pensthiel/head-md-future-of-drawing/electronics/fritzing/shematic_schem.jpg

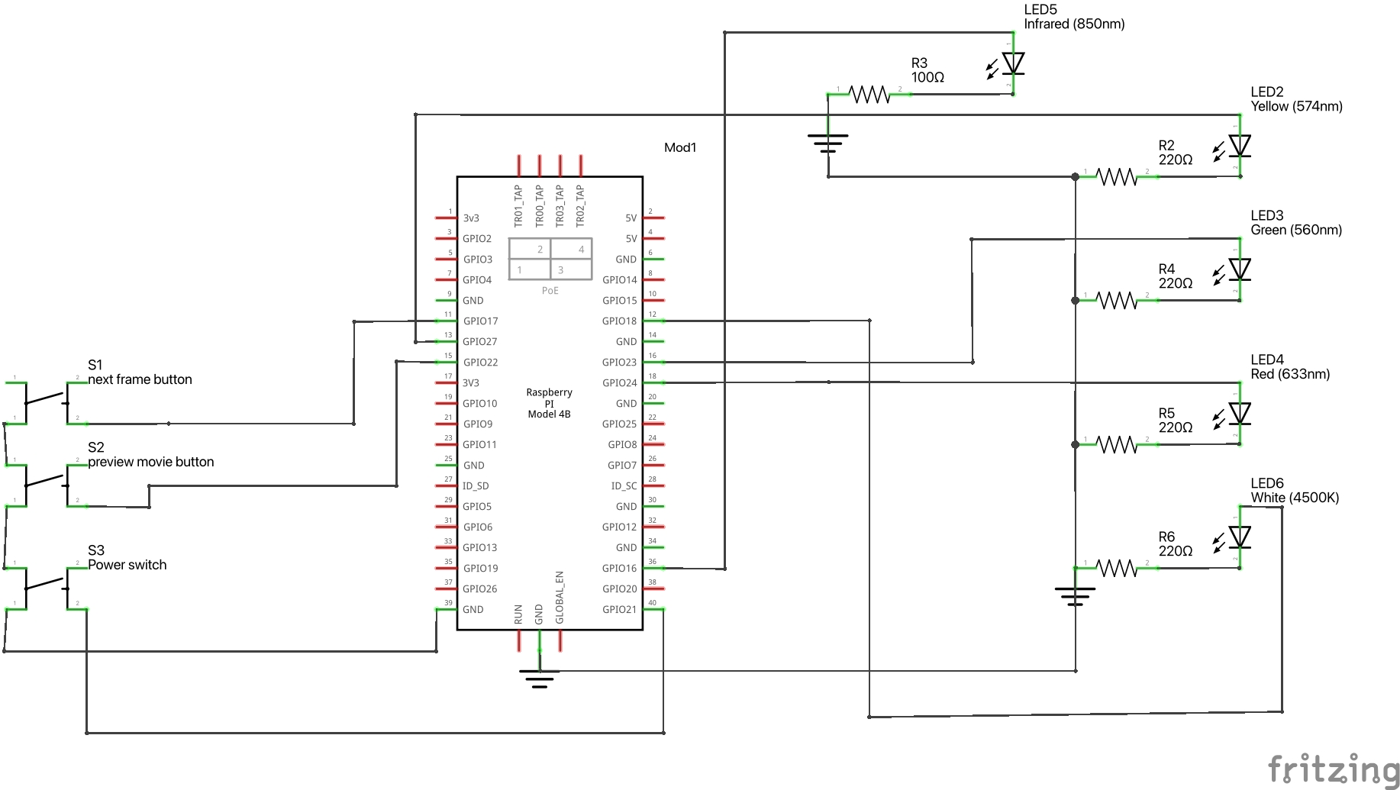
electronics/fritzing/shematic_schem.jpg
