pensthiel/head-md-future-of-drawing/electronics/photos/img_1540.jpg

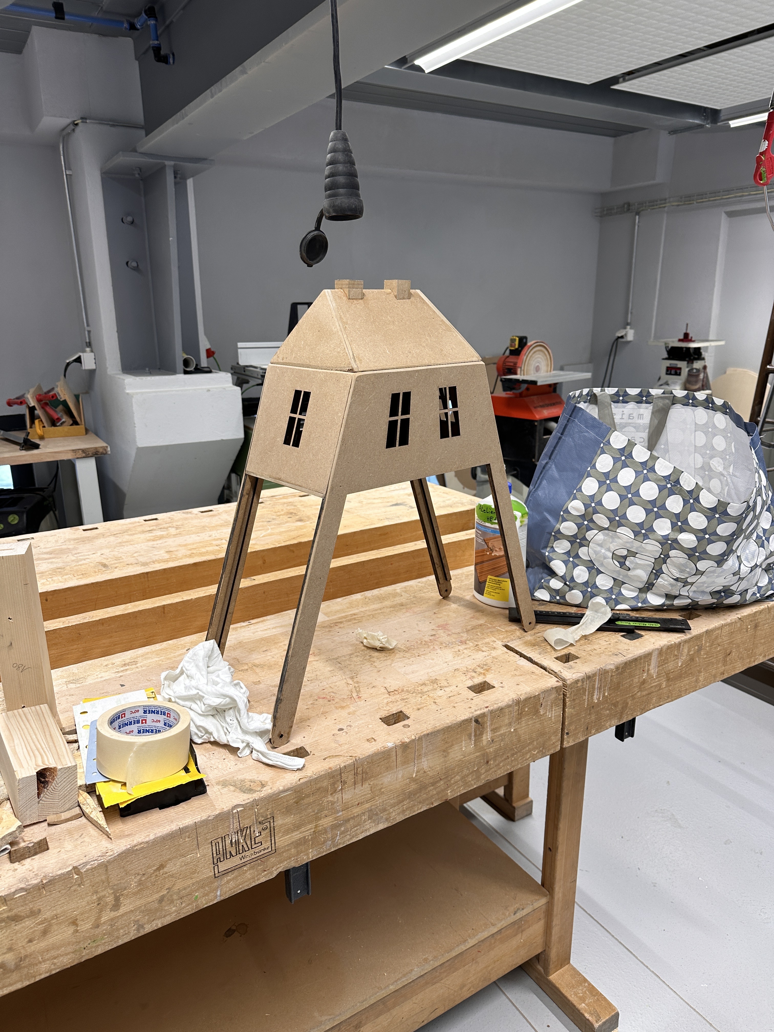
electronics/photos/img_1540.jpg
