pensthiel/head-md-future-of-drawing/electronics/photos/img_1547.jpg

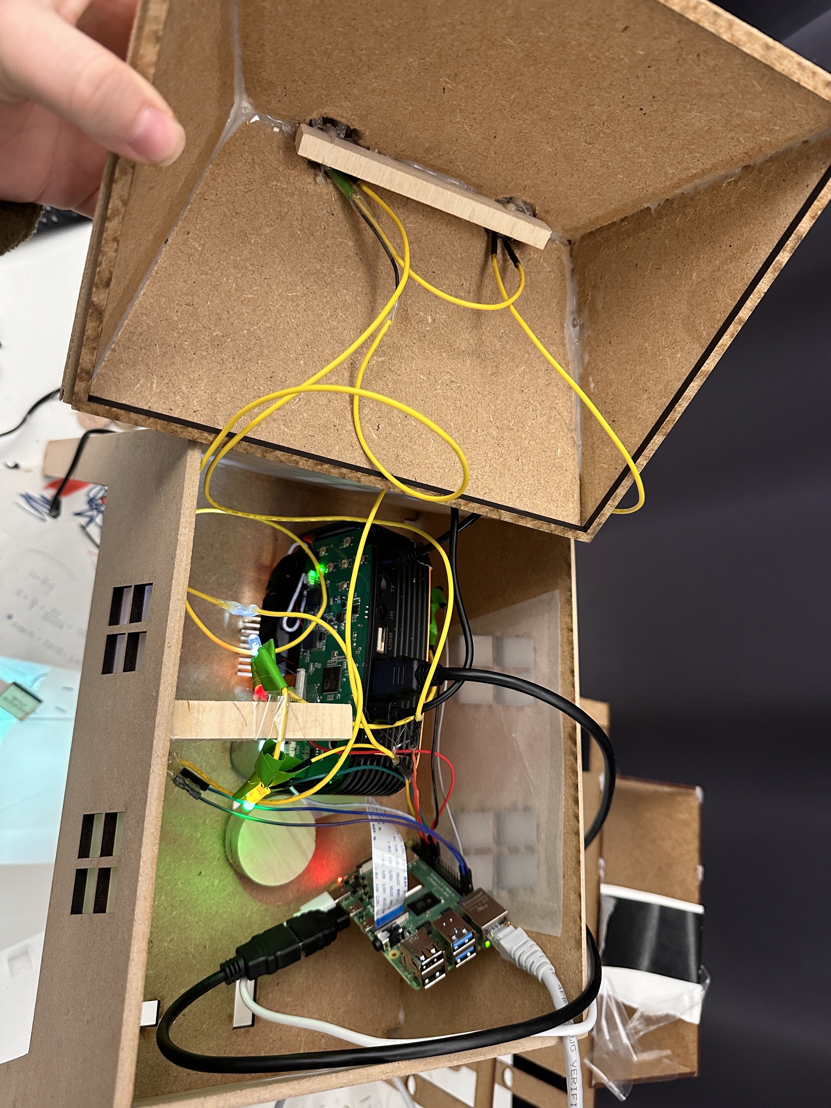
electronics/photos/img_1547.jpg
