pensthiel/head-md-future-of-drawing/expo/3d/Screenshot 2024-03-19 at 19.50.46.png

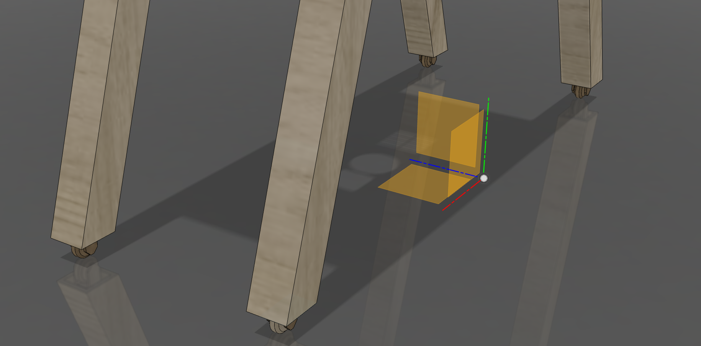
expo/3d/Screenshot 2024-03-19 at 19.50.46.png
