pensthiel/head-md-future-of-drawing/expo/3d/Screenshot 2024-03-19 at 19.51.49.png

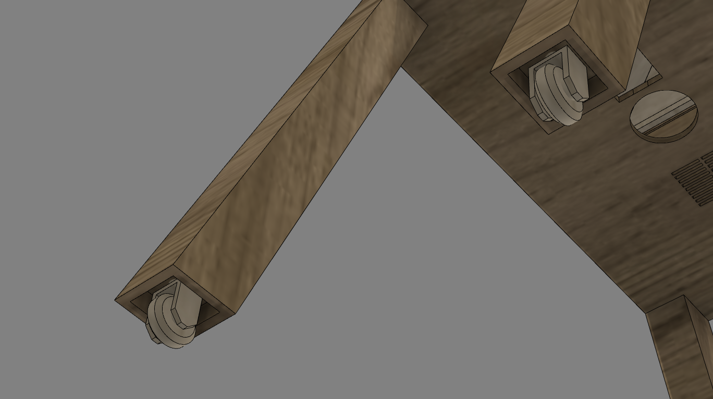
expo/3d/Screenshot 2024-03-19 at 19.51.49.png
