pensthiel/head-md-future-of-drawing/expo/3d/Screenshot 2024-03-19 at 19.52.38.png

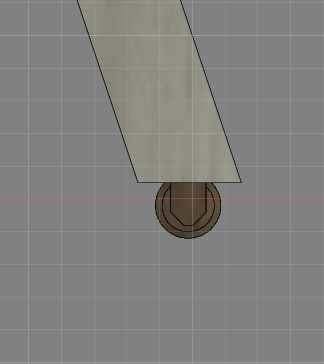
expo/3d/Screenshot 2024-03-19 at 19.52.38.png
