pensthiel/head-md-future-of-drawing/expo/3d/Screenshot 2024-03-20 at 10.05.37.png

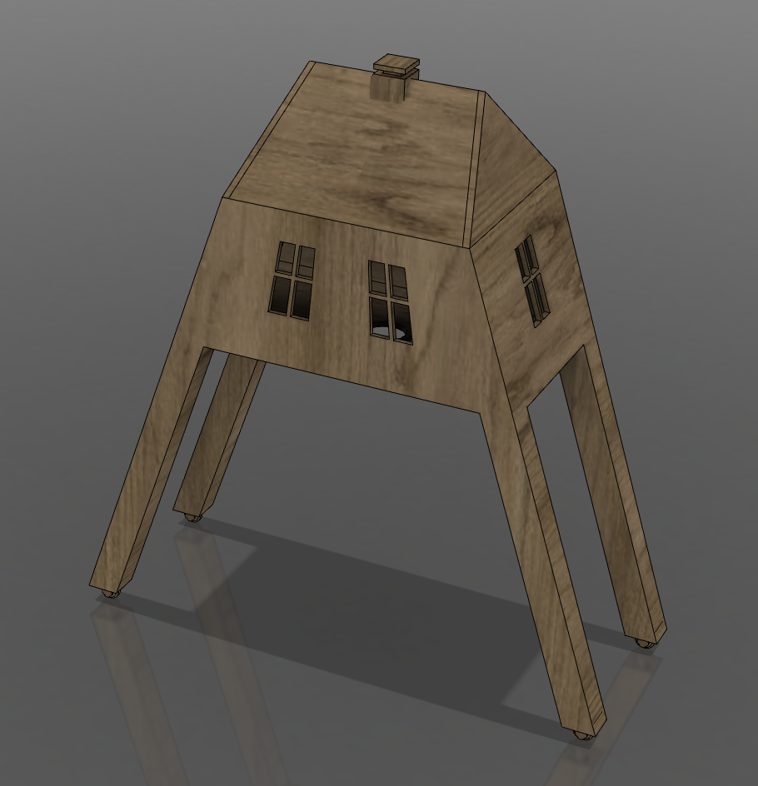
expo/3d/Screenshot 2024-03-20 at 10.05.37.png
