pensthiel/head-md-future-of-drawing/expo/3d/Screenshot 2024-04-22 at 10.32.50.png

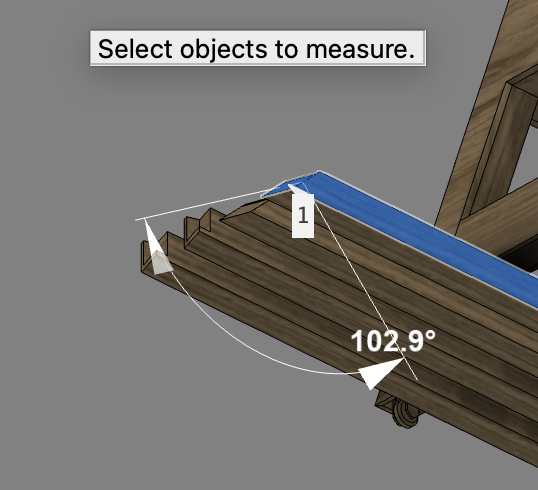
expo/3d/Screenshot 2024-04-22 at 10.32.50.png
