pensthiel/head-md-future-of-drawing/expo/shema/Untitled_Artwork.jpg

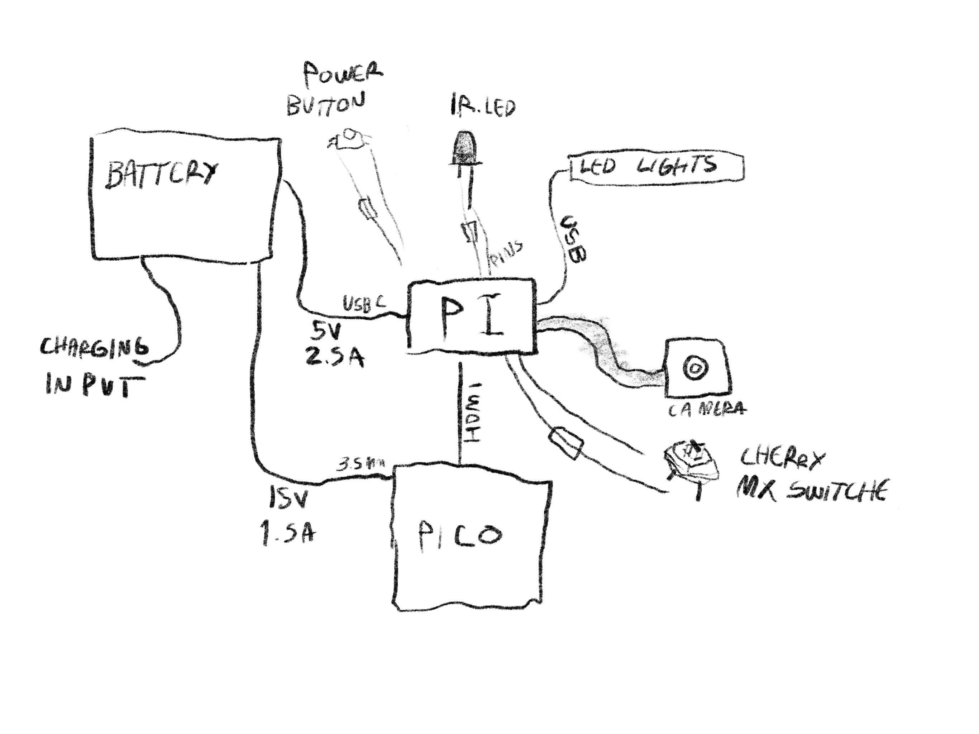
expo/shema/Untitled_Artwork.jpg
