pensthiel/head-md-future-of-drawing/namur/IMG_6740.jpg

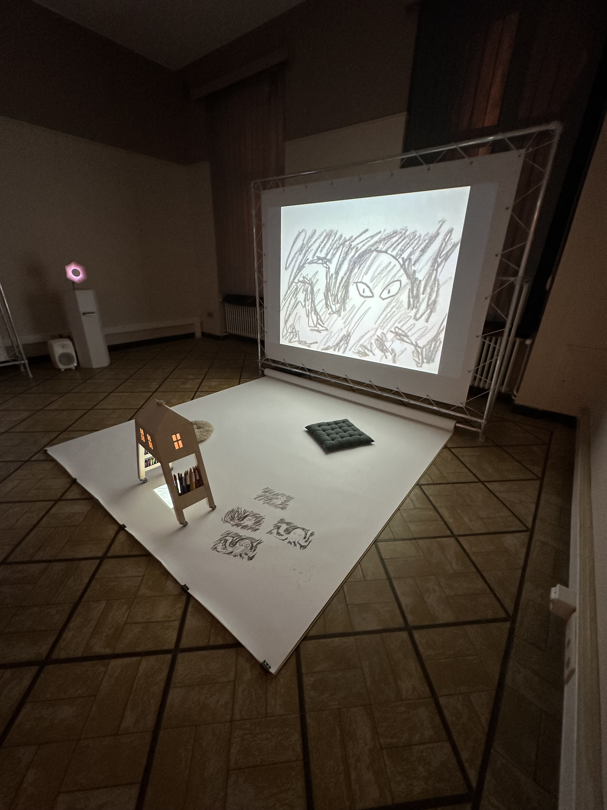
namur/IMG_6740.jpg
