pensthiel/head-md-future-of-drawing/namur/IMG_6743.jpg

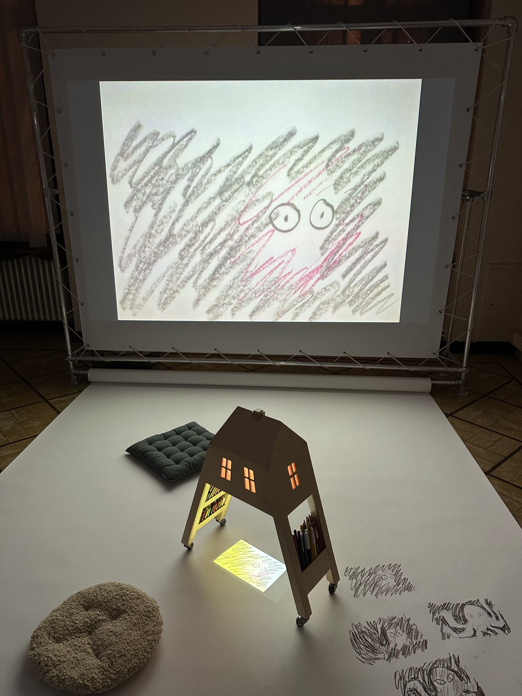
namur/IMG_6743.jpg
