pensthiel/head-md-future-of-drawing/namur/IMG_6744.jpg

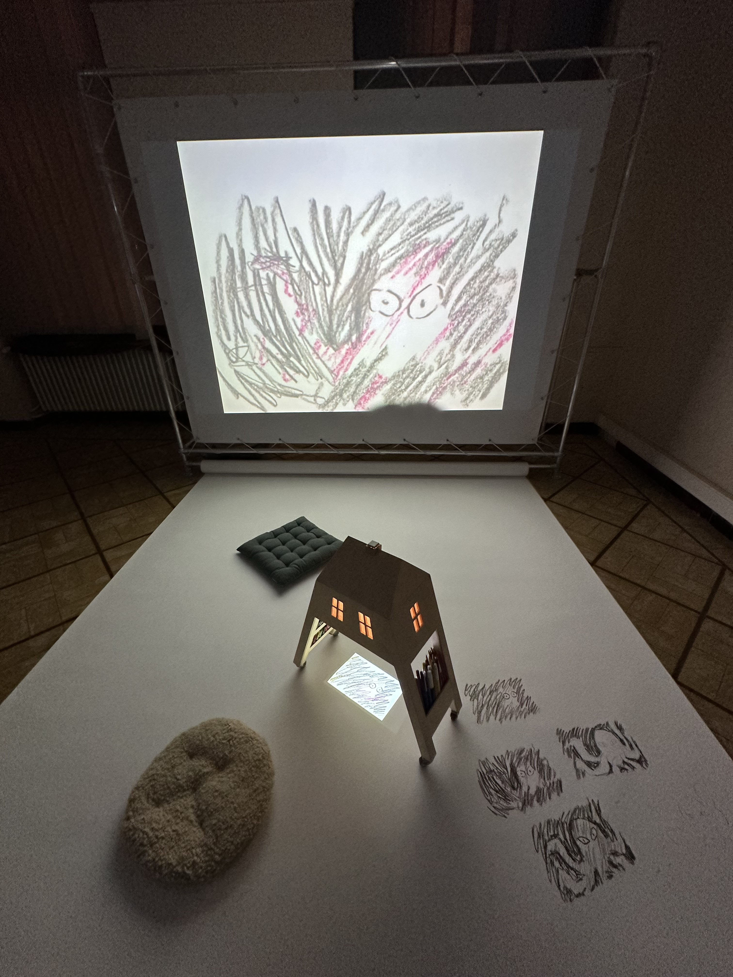
namur/IMG_6744.jpg
