pensthiel/head-md-future-of-drawing/namur/IMG_6754.jpg

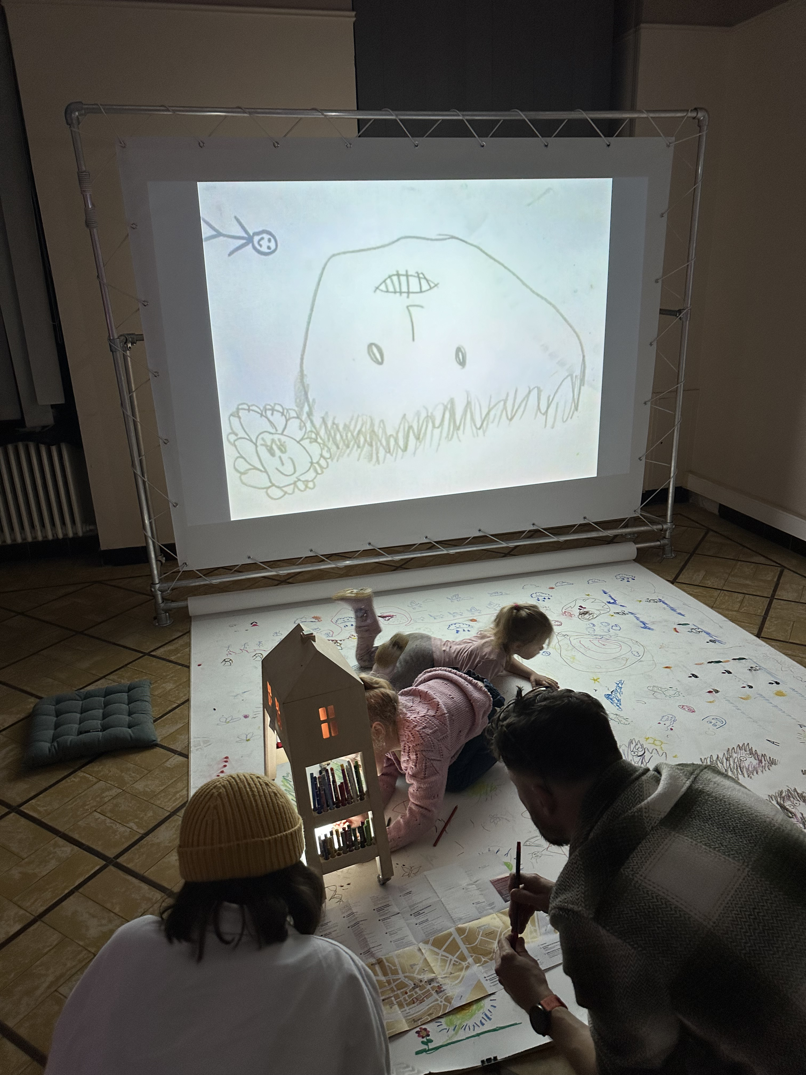
namur/IMG_6754.jpg
