pensthiel/head-md-future-of-drawing/namur/IMG_6794.jpg

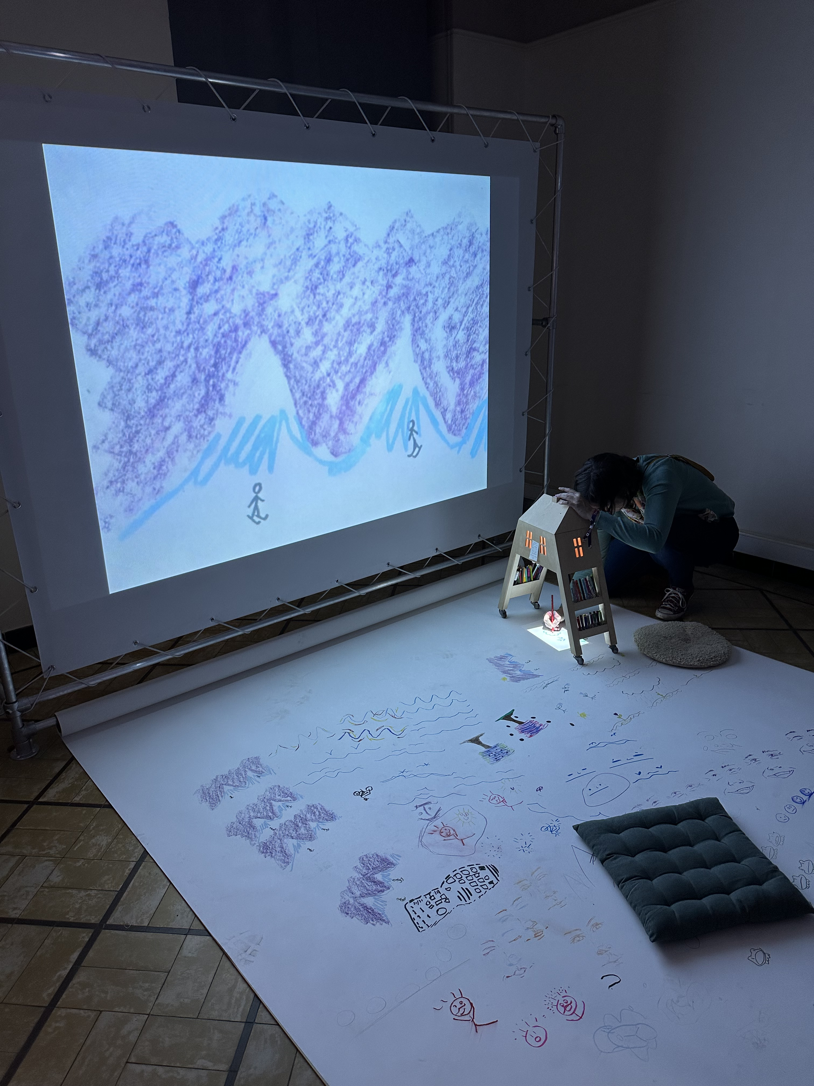
namur/IMG_6794.jpg
