pensthiel/head-md-future-of-drawing/namur/IMG_6797.jpg

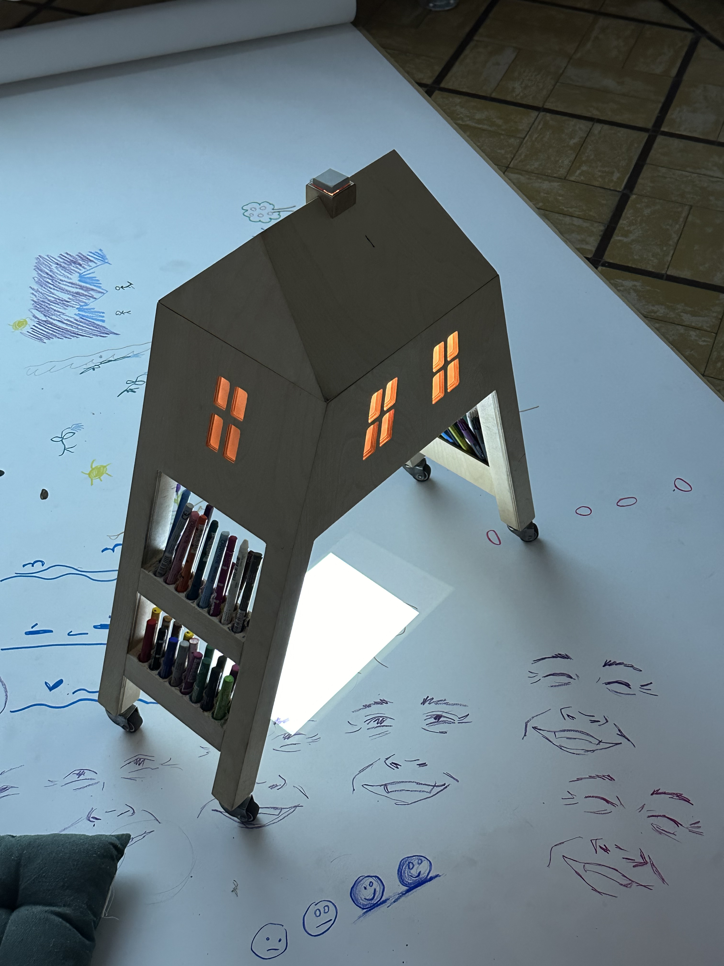
namur/IMG_6797.jpg
