pensthiel/head-md-future-of-drawing/namur/IMG_6829.jpg

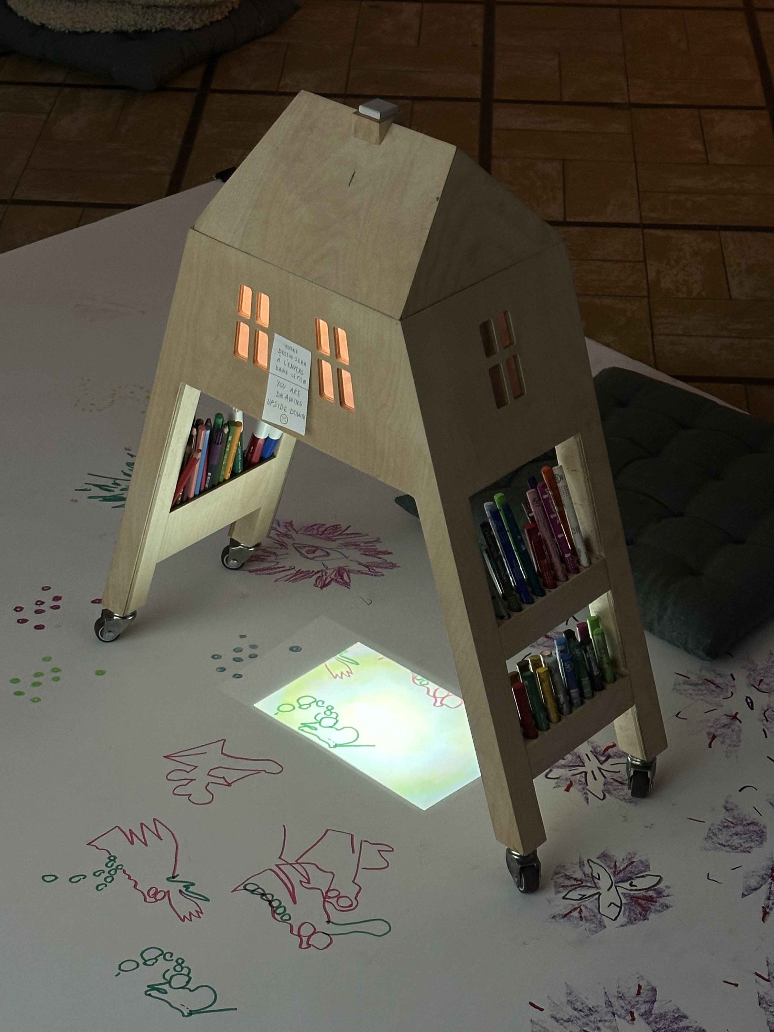
namur/IMG_6829.jpg
