pensthiel/head-md-future-of-drawing/namur/IMG_6830.jpg

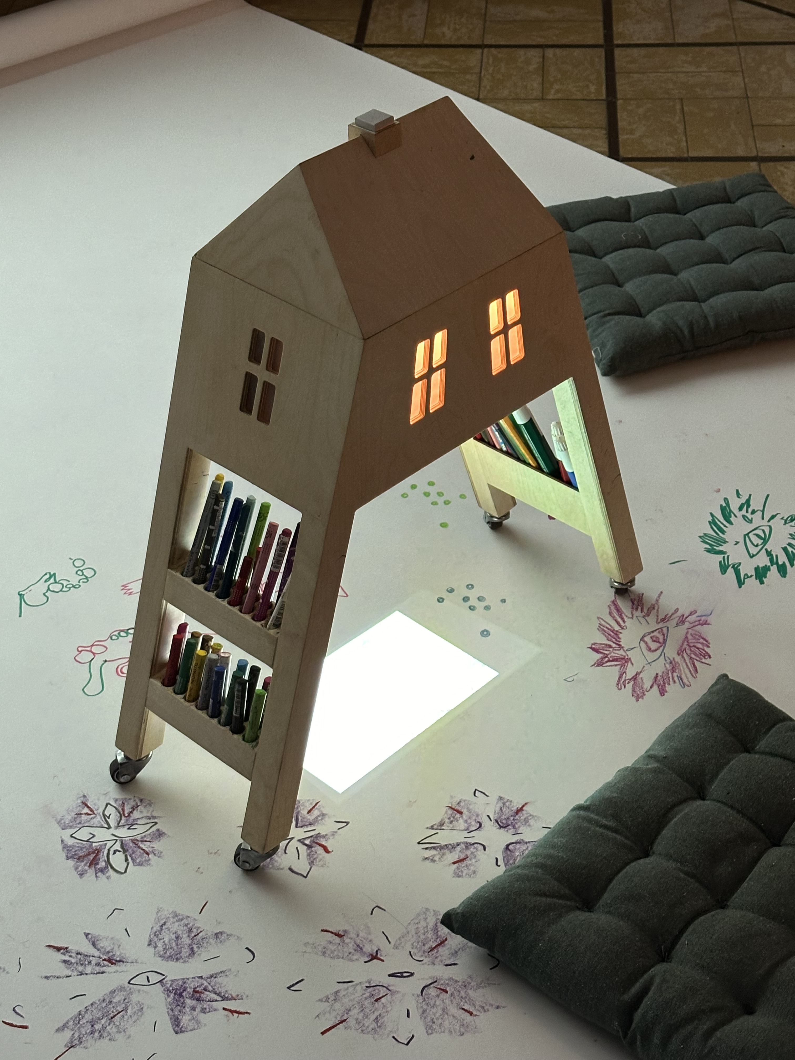
namur/IMG_6830.jpg
