pensthiel/head-md-future-of-drawing/namur/IMG_6961.jpg

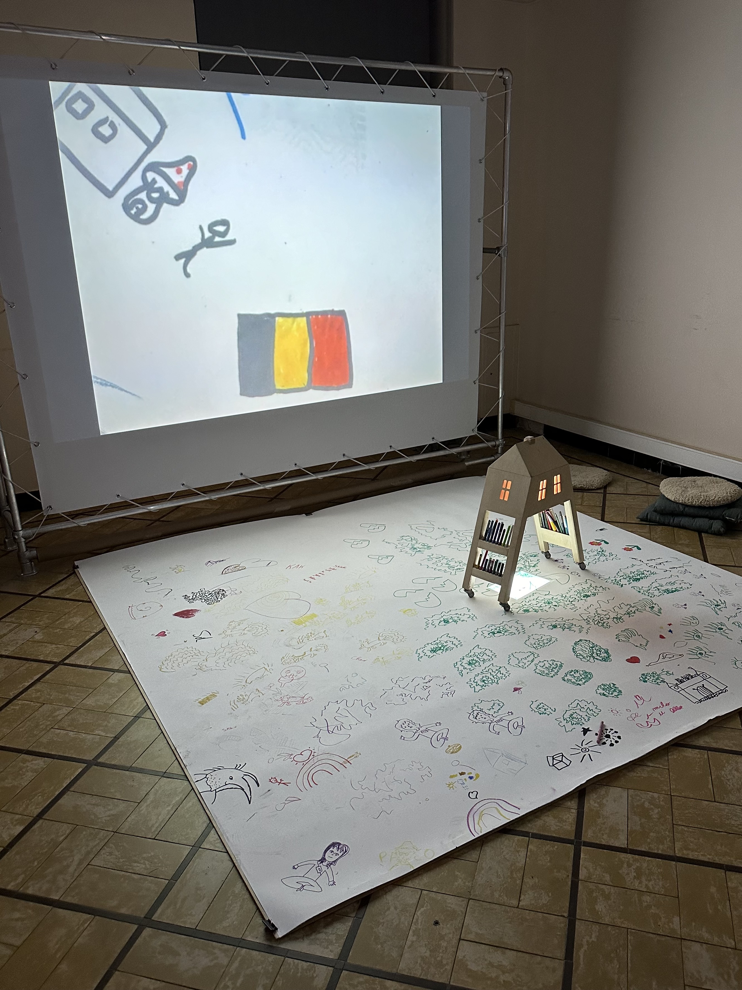
namur/IMG_6961.jpg
