pensthiel/head-md-future-of-drawing/namur/IMG_6975.jpg

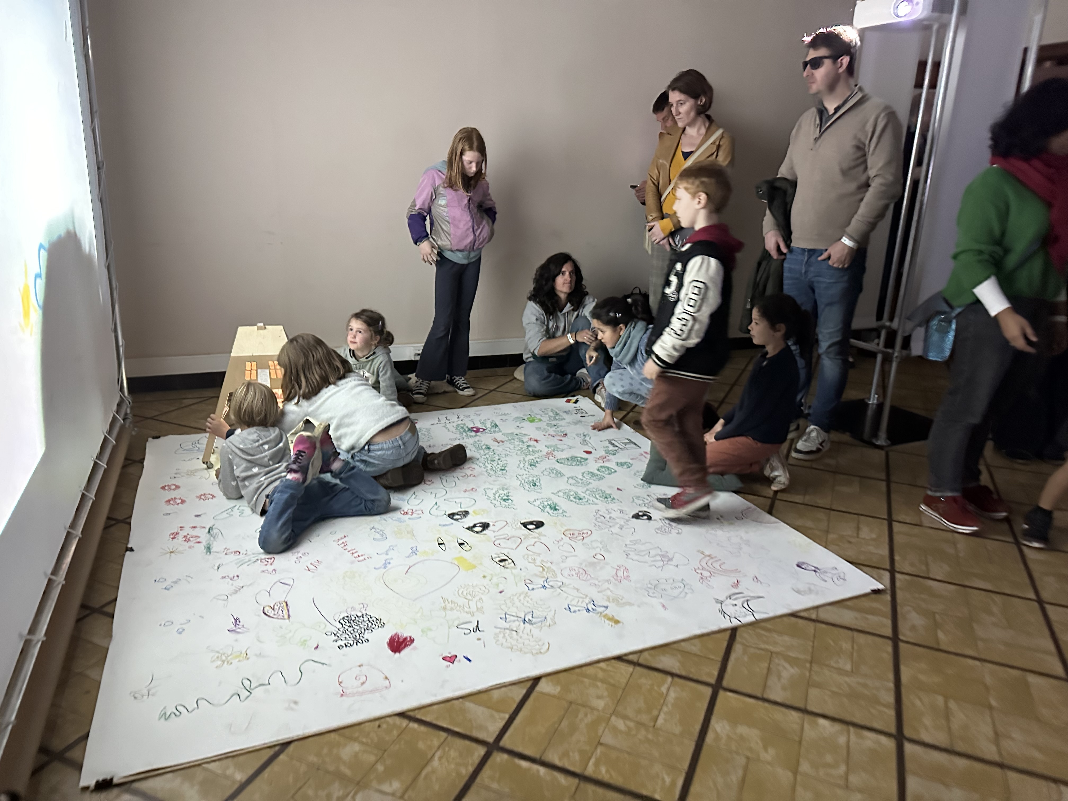
namur/IMG_6975.jpg
