pensthiel/head-md-future-of-drawing/object/export/form-render.jpg

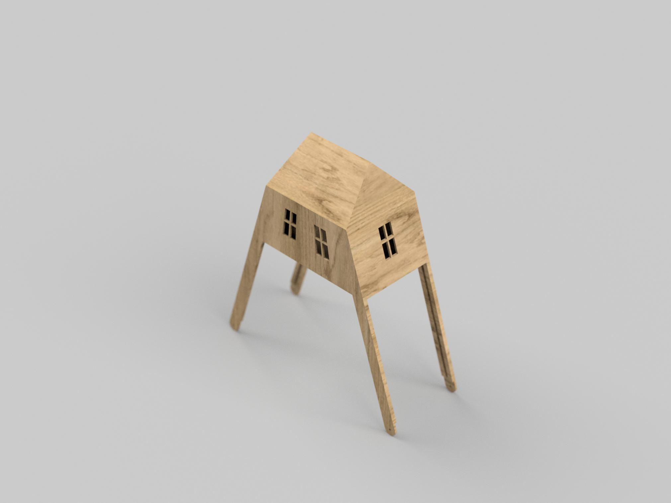
object/export/form-render.jpg
