pensthiel/head-md-future-of-drawing/object/export/Screenshot 2024-01-15 at 15.24.52.png

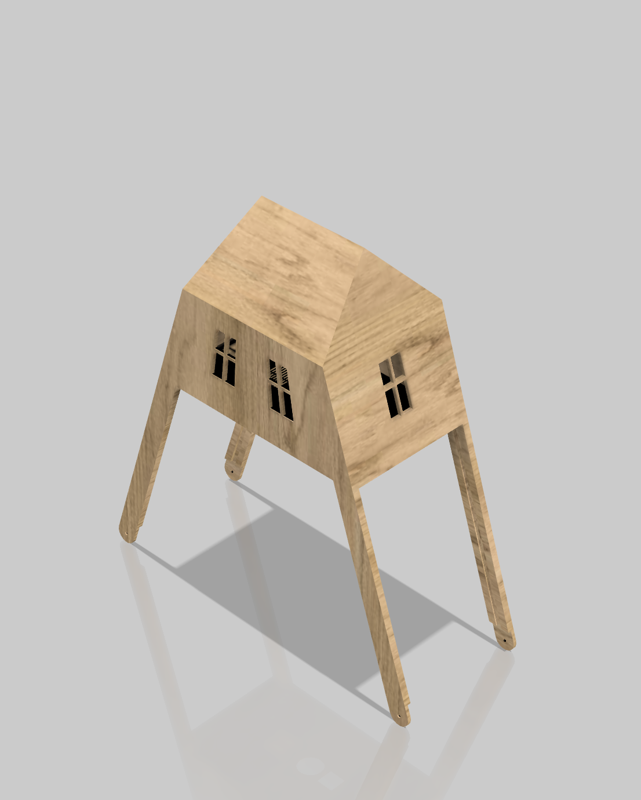
object/export/Screenshot 2024-01-15 at 15.24.52.png
