pensthiel/head-md-future-of-drawing/object/export/Screenshot 2024-01-15 at 21.01.21.png

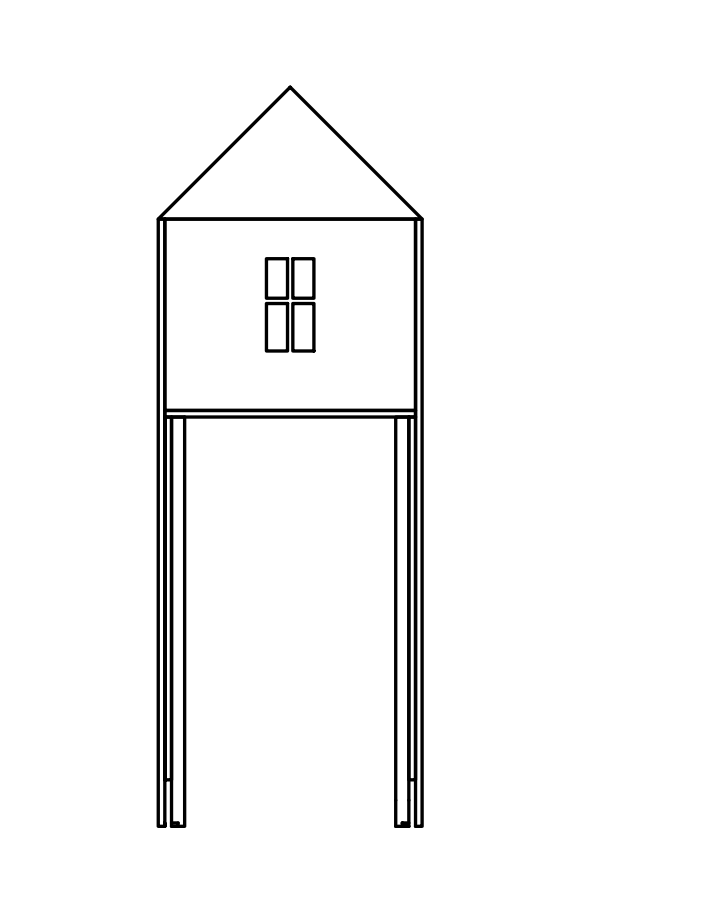
object/export/Screenshot 2024-01-15 at 21.01.21.png
