pensthiel/head-md-future-of-drawing/object/export/Screenshot 2024-01-15 at 21.01.27.png

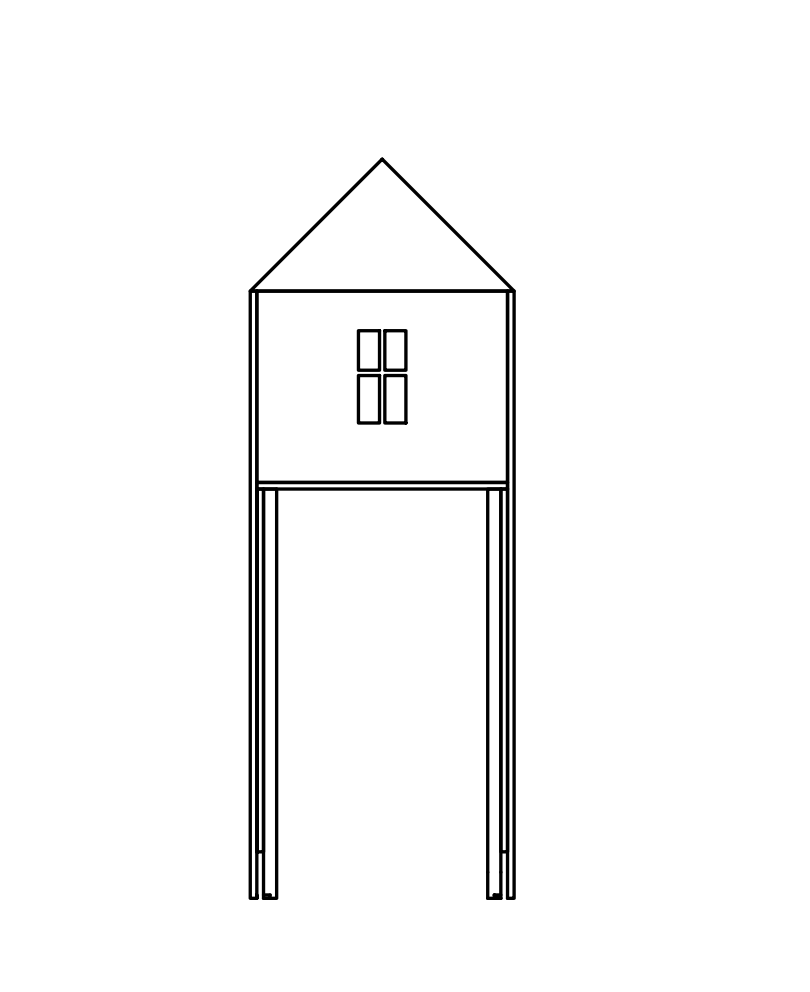
object/export/Screenshot 2024-01-15 at 21.01.27.png
