pensthiel/head-md-future-of-drawing/object/photos/IMG_1553 2.JPG

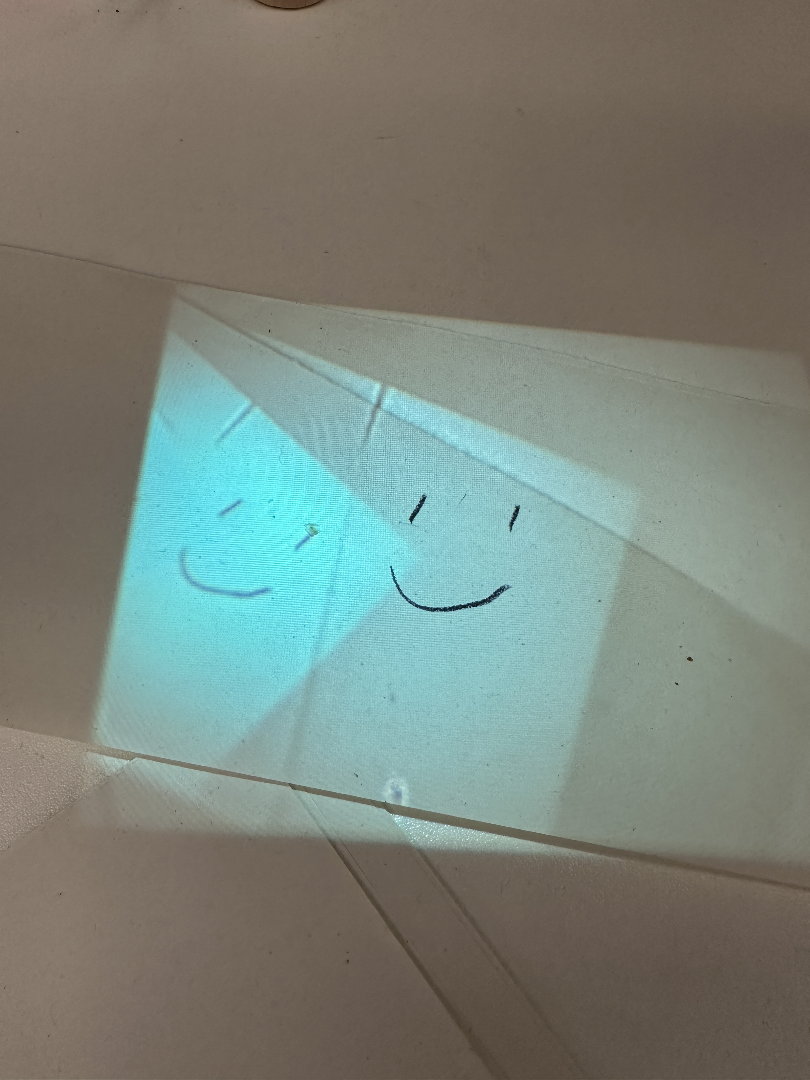
object/photos/IMG_1553 2.JPG
