pensthiel/head-md-future-of-drawing/object/photos/IMG_1554.JPG

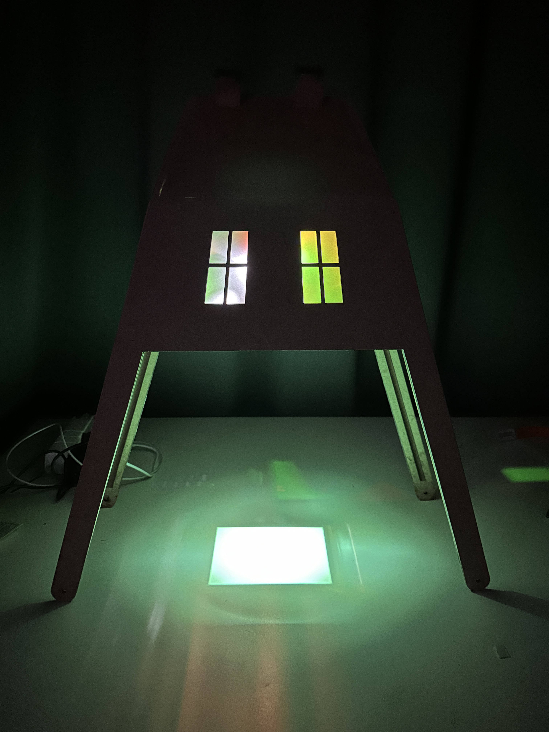
object/photos/IMG_1554.JPG
