pensthiel/head-md-future-of-drawing/object/photos/IMG_1555.JPG

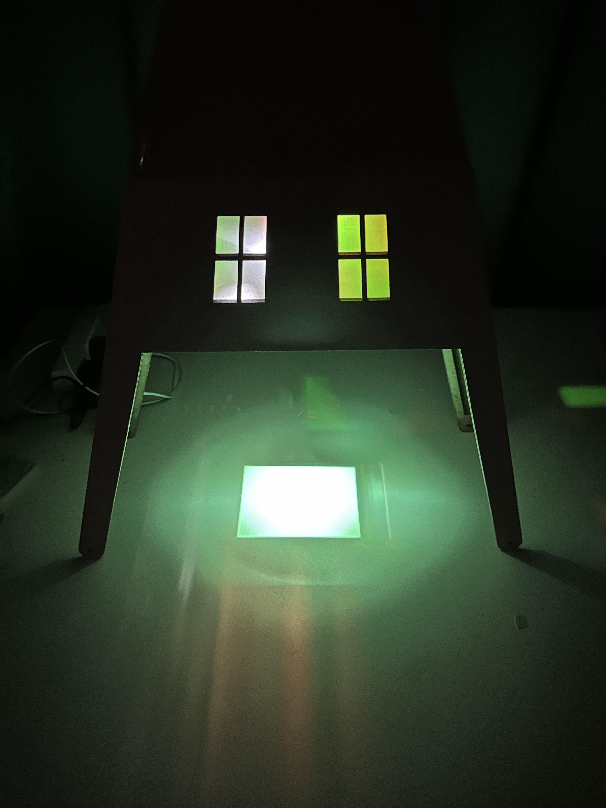
object/photos/IMG_1555.JPG
