pensthiel/head-md-future-of-drawing/object/photos/IMG_1556.JPG

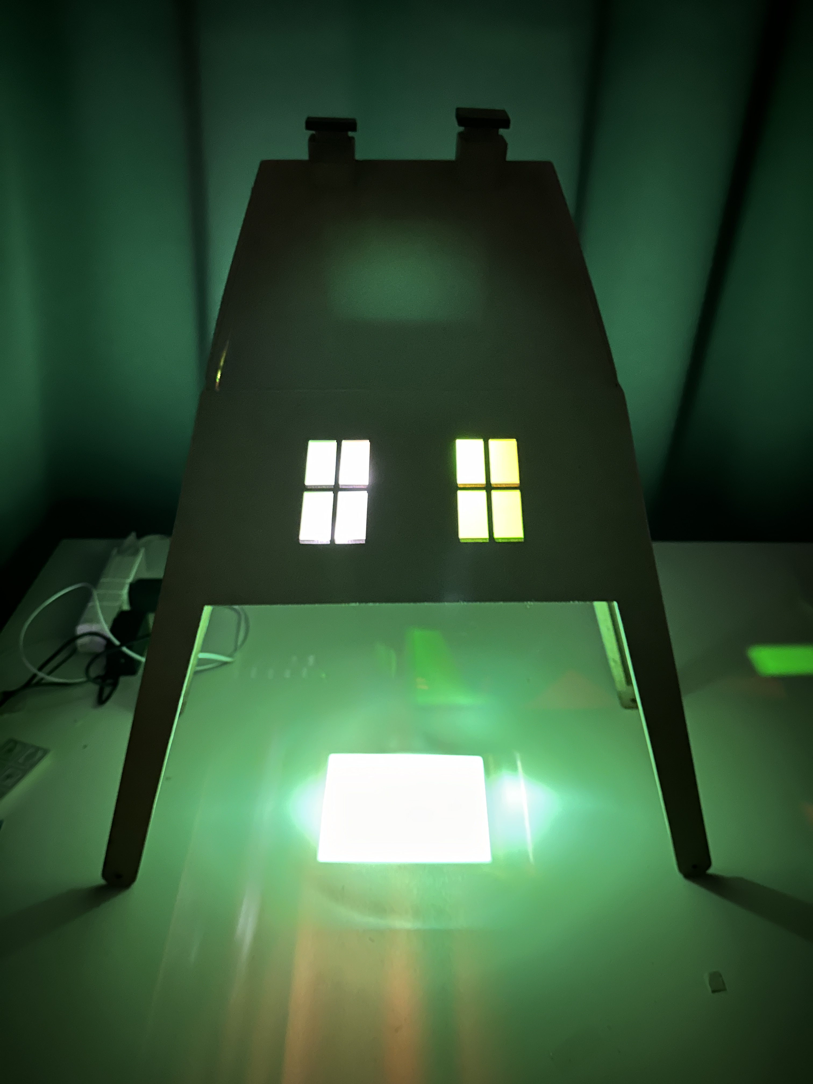
object/photos/IMG_1556.JPG
