pensthiel/head-md-future-of-drawing/object/photos/IMG_1558.JPG

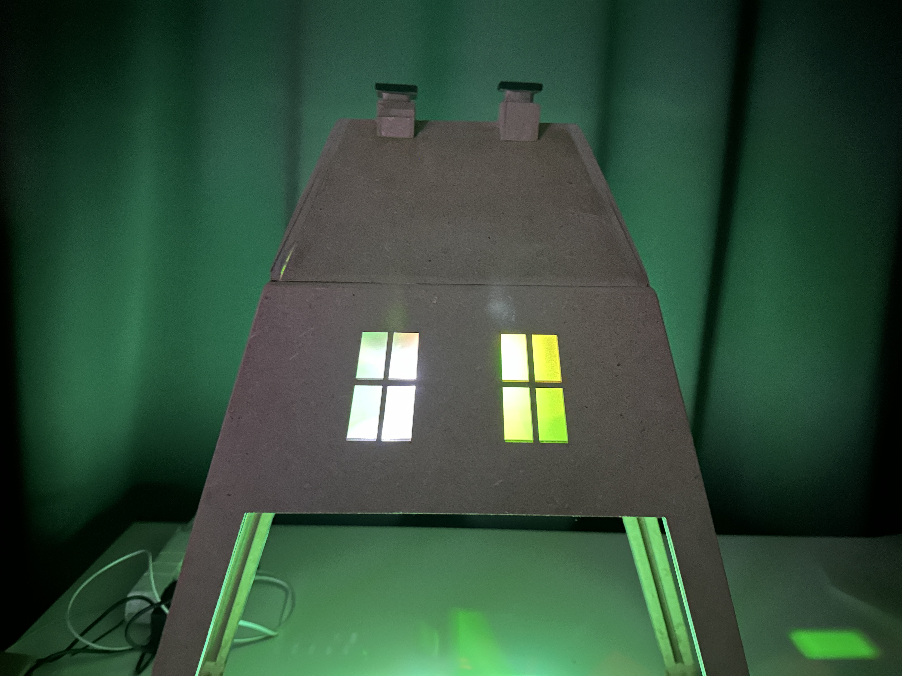
object/photos/IMG_1558.JPG
