pensthiel/head-md-future-of-drawing/object/photos/IMG_1559.JPG

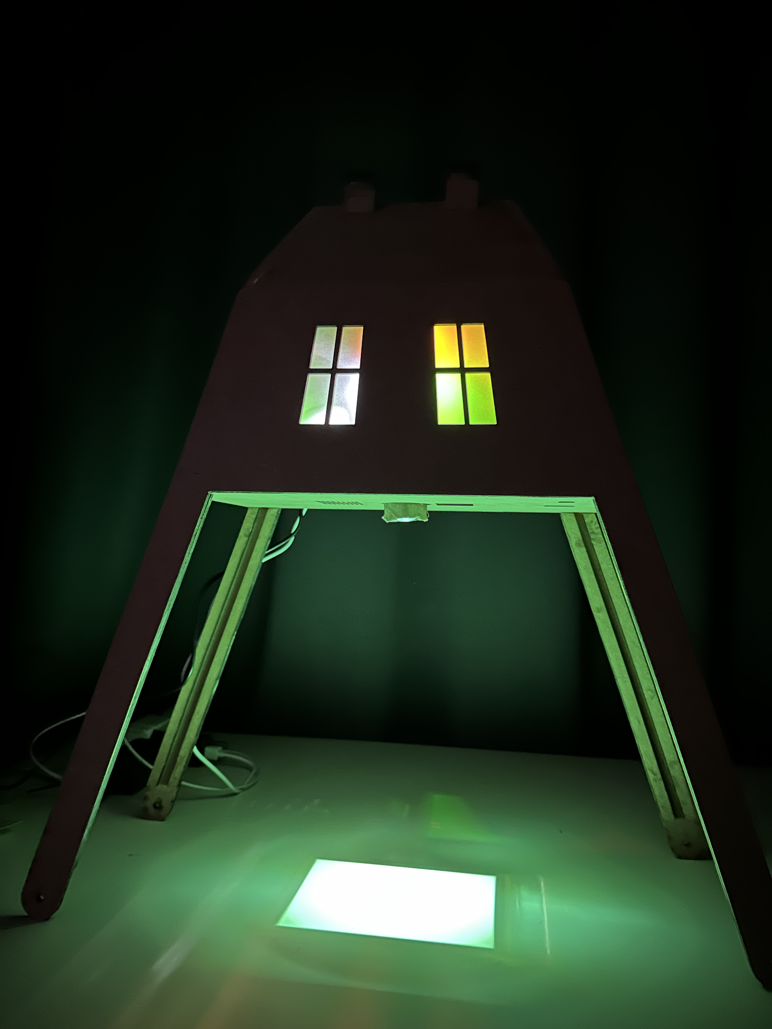
object/photos/IMG_1559.JPG
