pensthiel/head-md-future-of-drawing/object/photos/IMG_1560.JPG

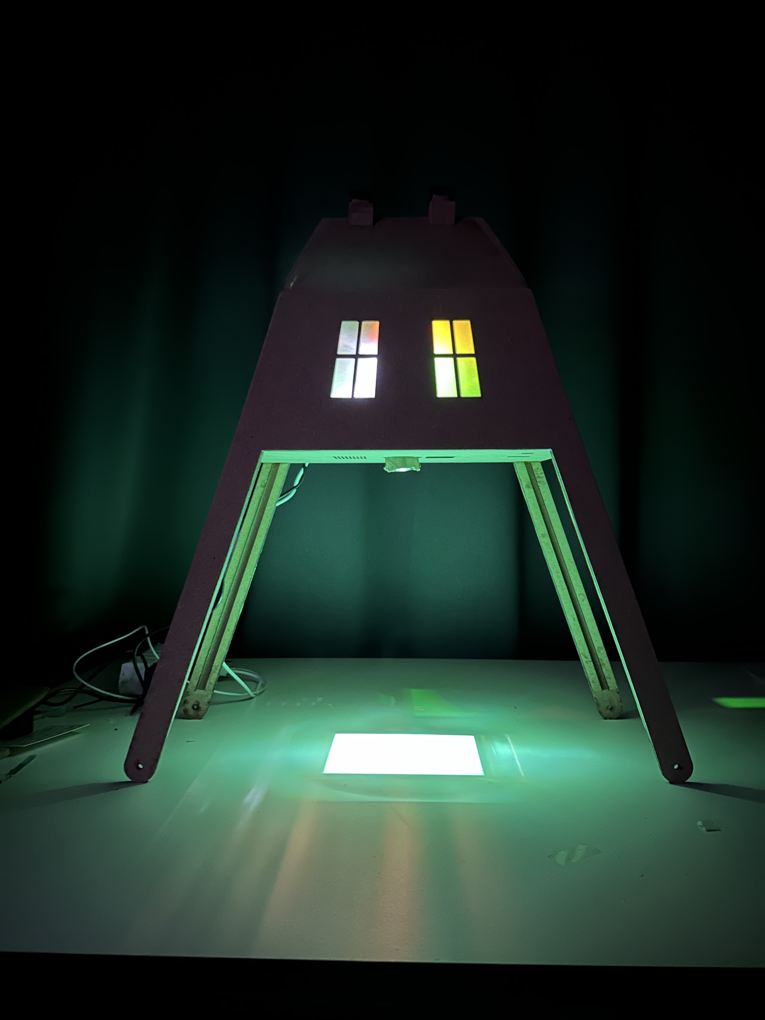
object/photos/IMG_1560.JPG
