pensthiel/head-md-future-of-drawing/object/photos/IMG_1561.JPG

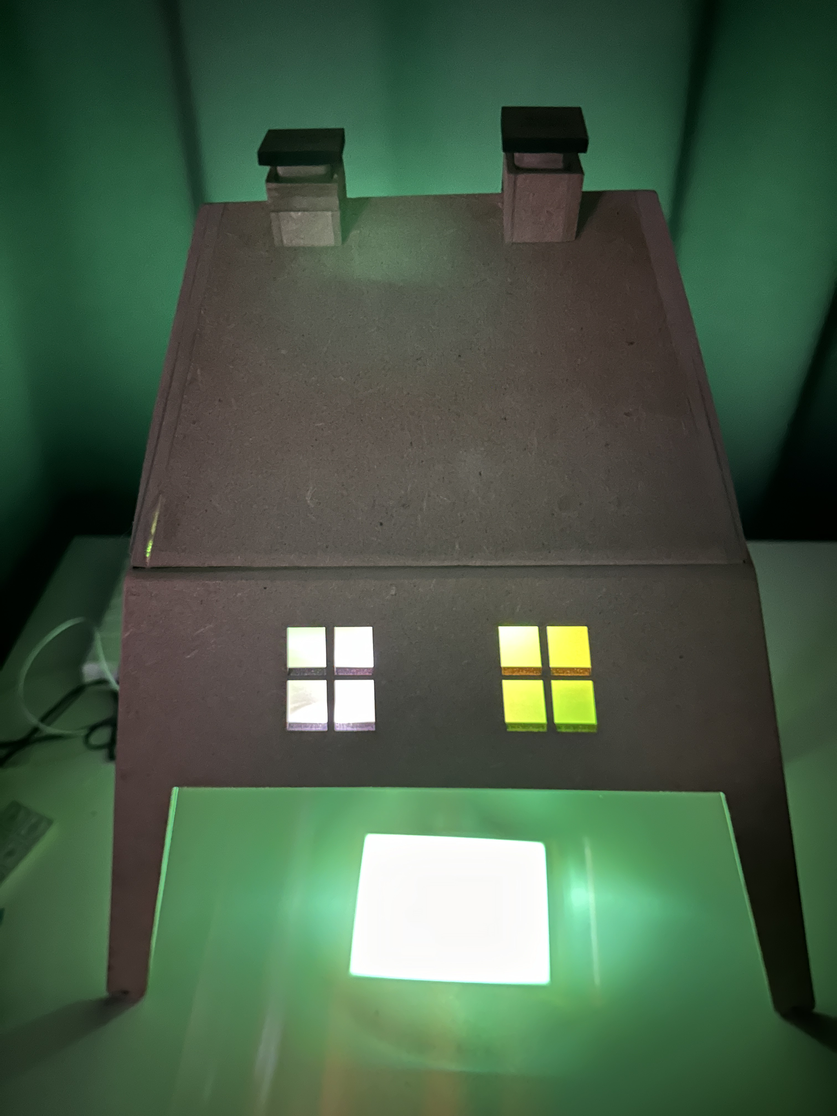
object/photos/IMG_1561.JPG
