pensthiel/head-md-future-of-drawing/object/photos/IMG_1563.JPG

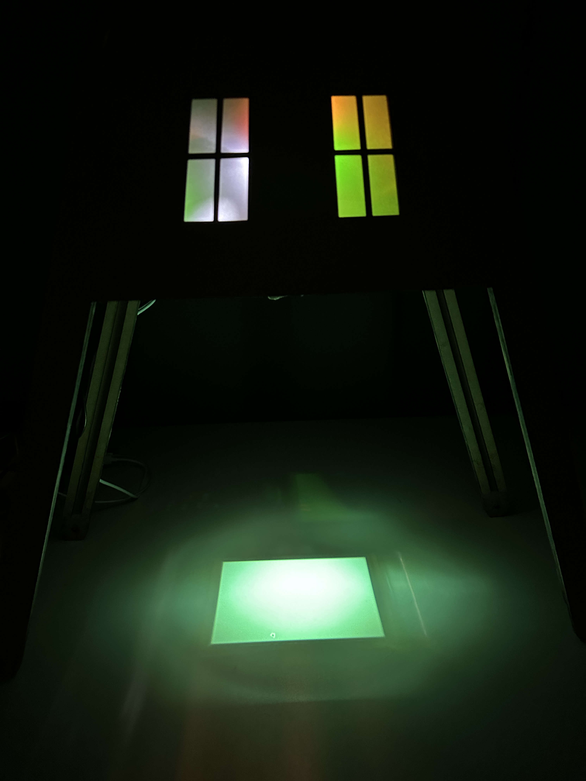
object/photos/IMG_1563.JPG
