pensthiel/head-md-future-of-drawing/object/photos/IMG_1564.JPG

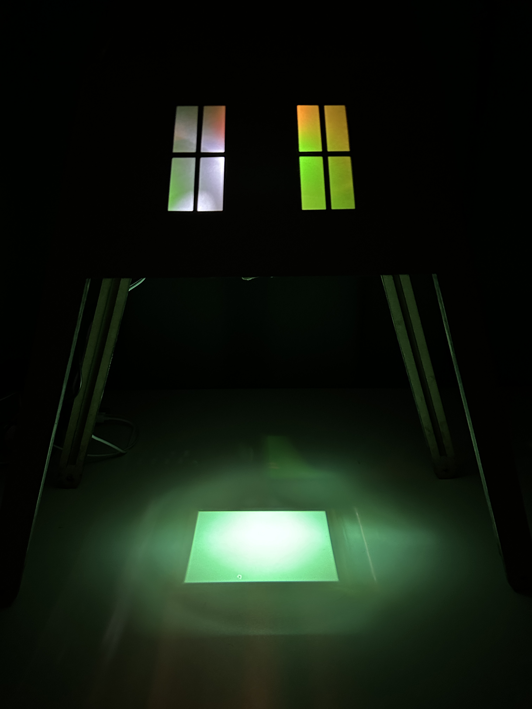
object/photos/IMG_1564.JPG
