pensthiel/head-md-future-of-drawing/object/photos/IMG_1565.JPG

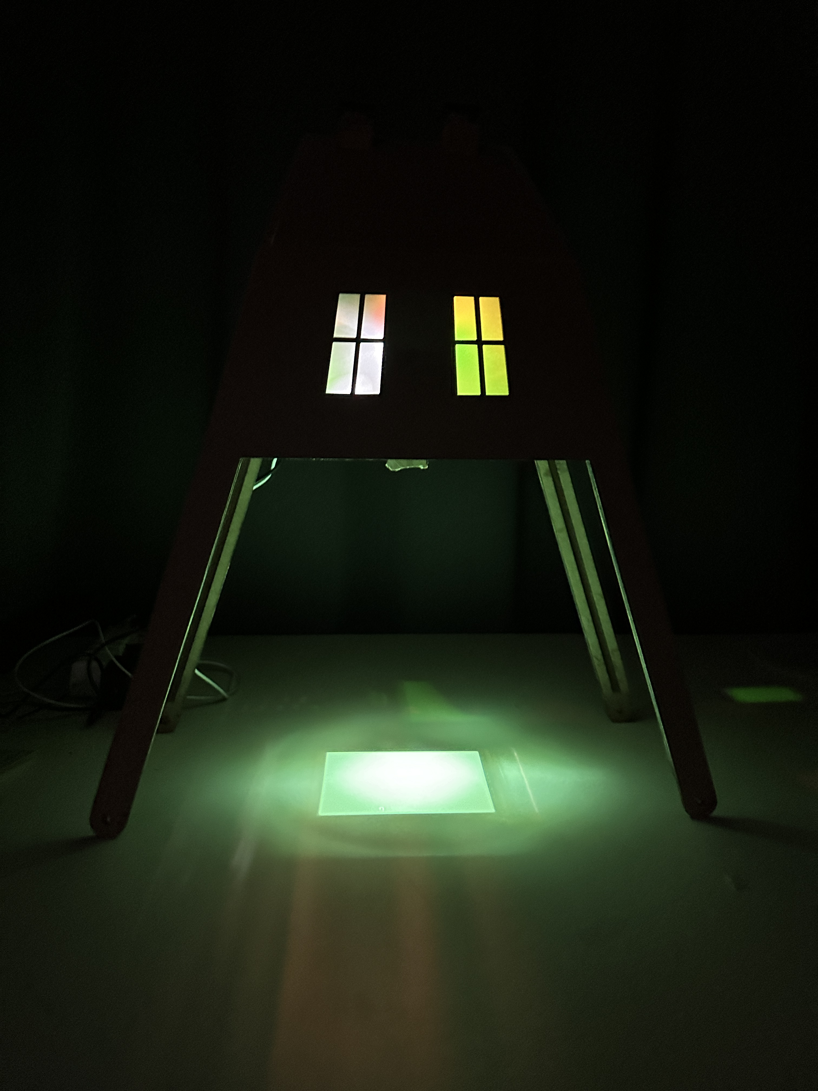
object/photos/IMG_1565.JPG
