pensthiel/head-md-future-of-drawing/object/photos/IMG_1568.JPG

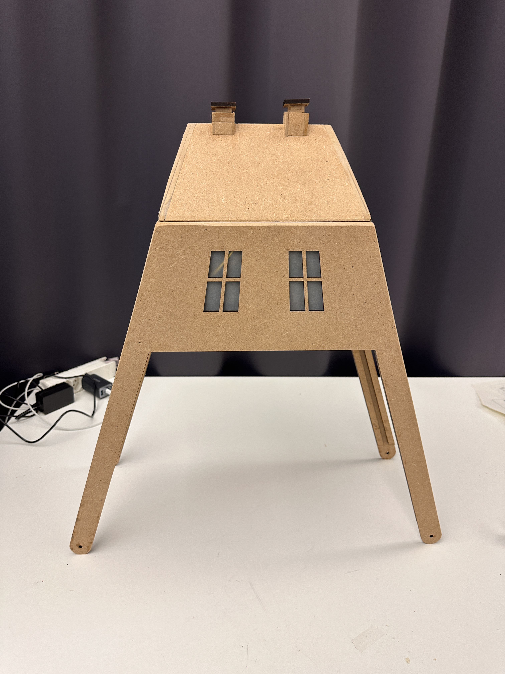
object/photos/IMG_1568.JPG
