pensthiel/head-md-future-of-drawing/object/photos/img_1573.jpg

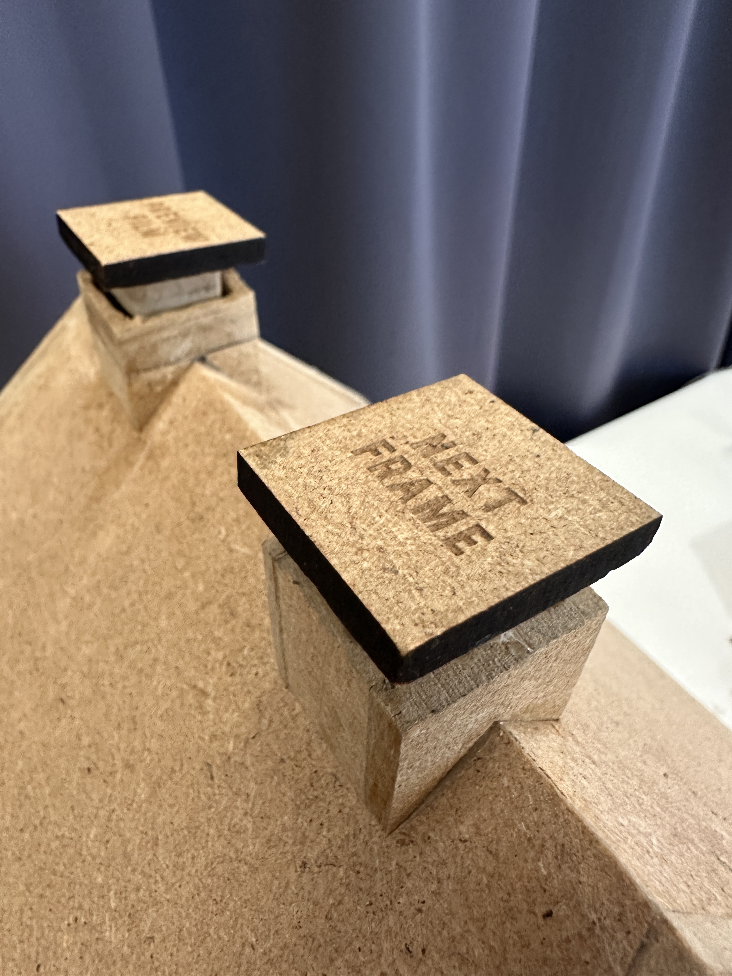
object/photos/img_1573.jpg
