pensthiel/head-md-future-of-drawing/object/photos/img_1574.jpg

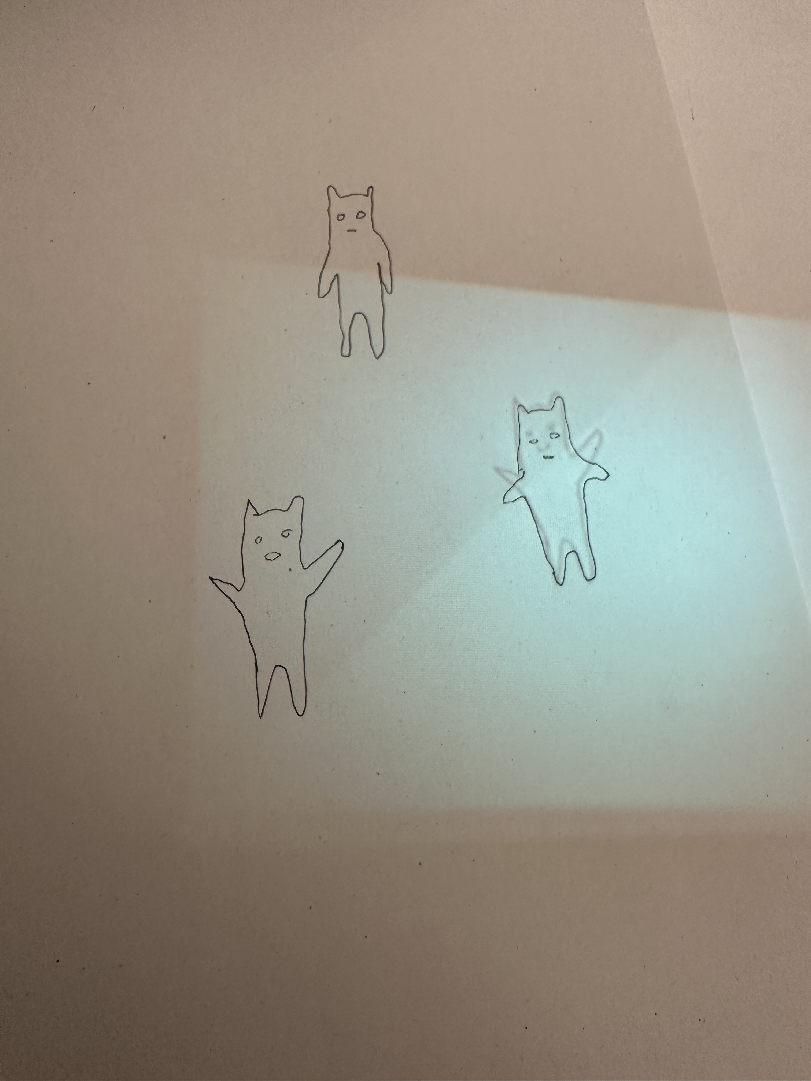
object/photos/img_1574.jpg
