pensthiel/head-md-future-of-drawing/object/photos/img_1575.jpg

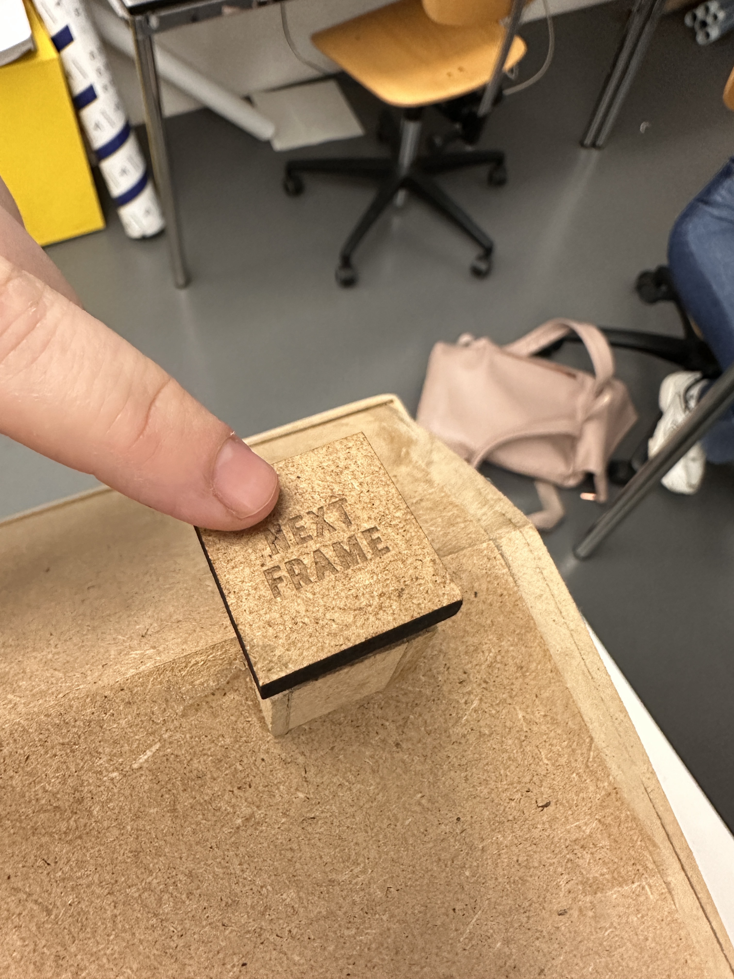
object/photos/img_1575.jpg
