pensthiel/head-md-future-of-drawing/object/photos/img_1576.jpg

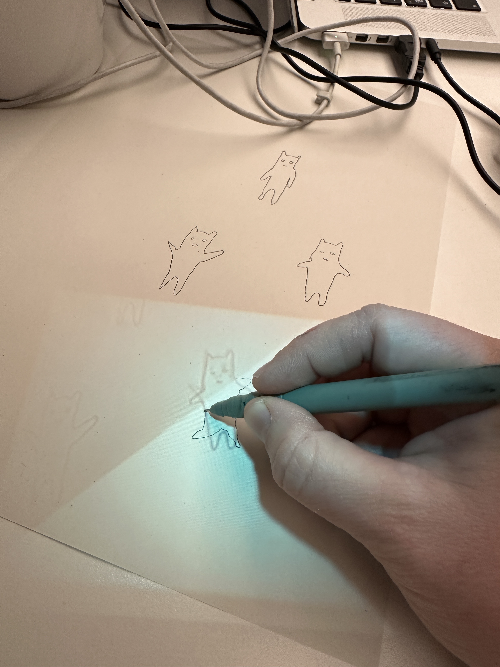
object/photos/img_1576.jpg
