pensthiel/head-md-future-of-drawing/object/photos/img_1582.jpg

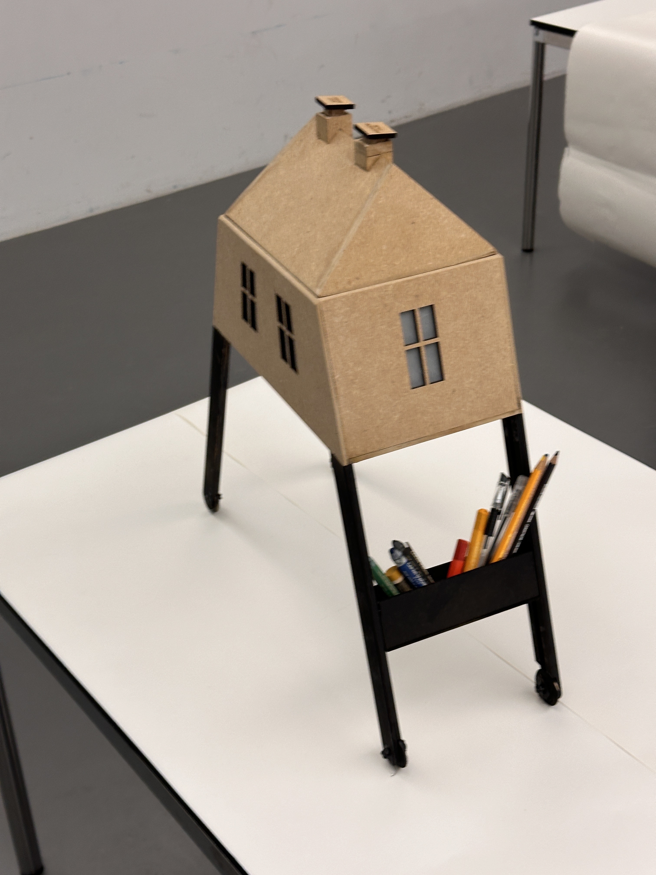
object/photos/img_1582.jpg
