pensthiel/head-md-future-of-drawing/object/photos/img_1585.jpg

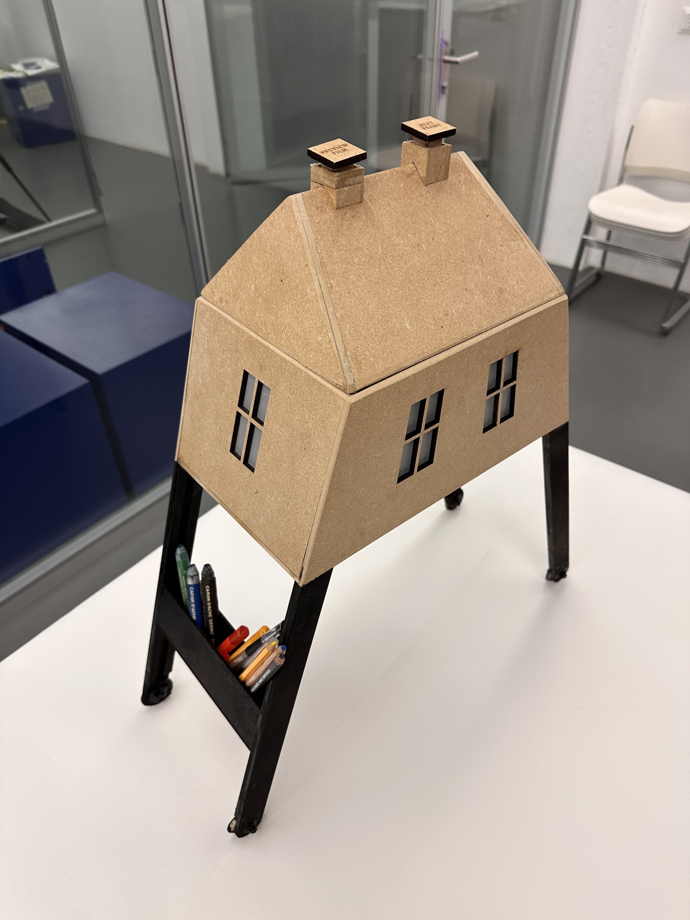
object/photos/img_1585.jpg
