pensthiel/head-md-future-of-drawing/object/refs/81t0O1HtNwL._AC_UF894,1000_QL80_.jpg

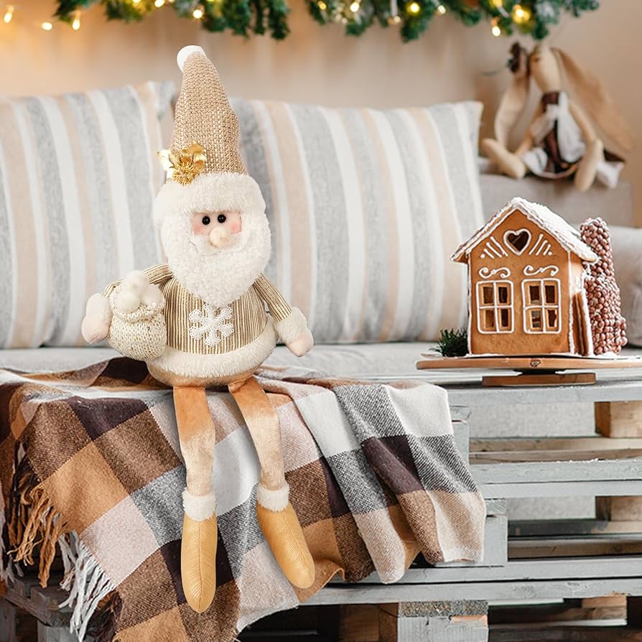
object/refs/81t0O1HtNwL._AC_UF894,1000_QL80_.jpg
