pensthiel/head-md-future-of-drawing/object/refs/360_F_519254240_TE0TRmz1se5YlQ5IMFw7UqPvs0KKaQv8.jpg

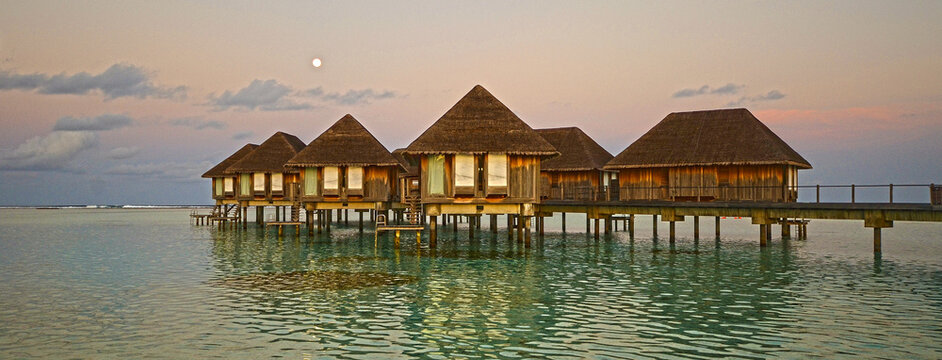
object/refs/360_F_519254240_TE0TRmz1se5YlQ5IMFw7UqPvs0KKaQv8.jpg
