pensthiel/head-md-future-of-drawing/object/refs/825b7a9ebf529b47e9a628f561fa0e20.jpg

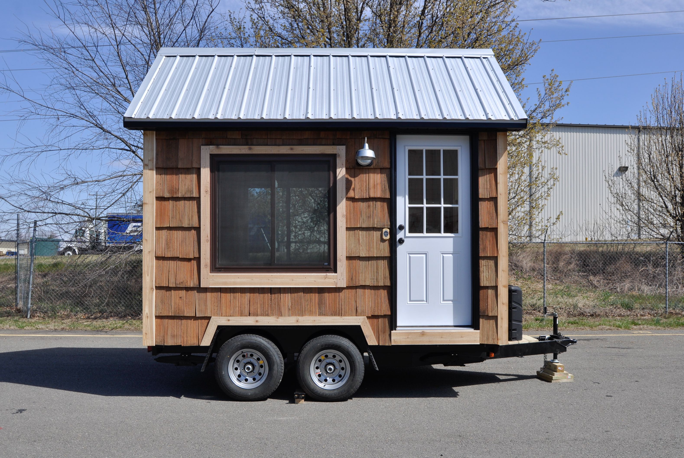
object/refs/825b7a9ebf529b47e9a628f561fa0e20.jpg
