pensthiel/head-md-future-of-drawing/object/refs/Lichthäuser-Großhandel-Weihnachten.webp

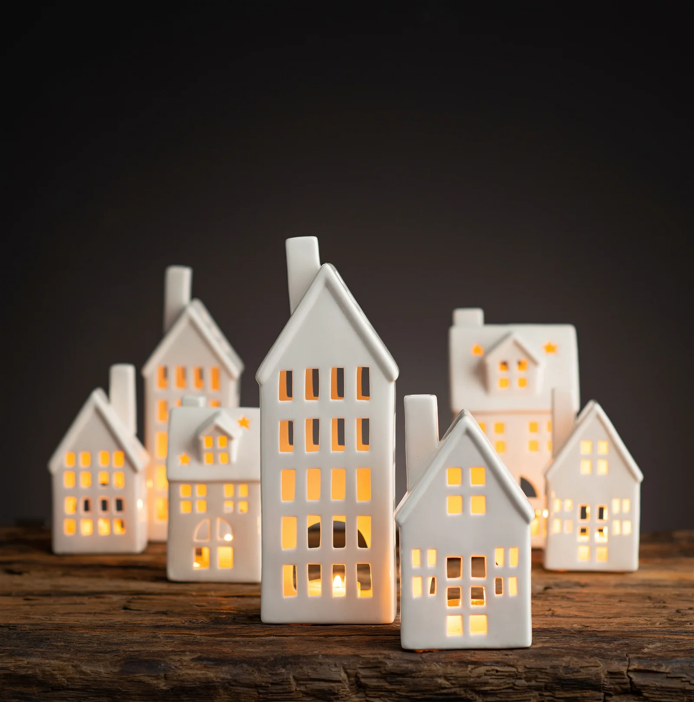
object/refs/Lichthäuser-Großhandel-Weihnachten.webp
