pensthiel/head-md-future-of-drawing/object/refs/main-qimg-66fd36552d90b1083be2a2db01242a83-lq.jpg

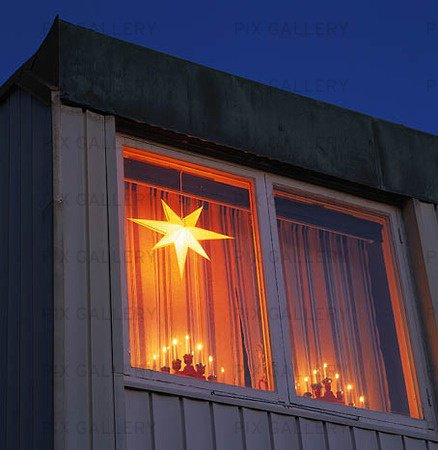
object/refs/main-qimg-66fd36552d90b1083be2a2db01242a83-lq.jpg
