pensthiel/head-md-future-of-drawing/object/refs/main-qimg-91e87c5d25ec91576e7c80ea1fdd794d-pjlq.jpg

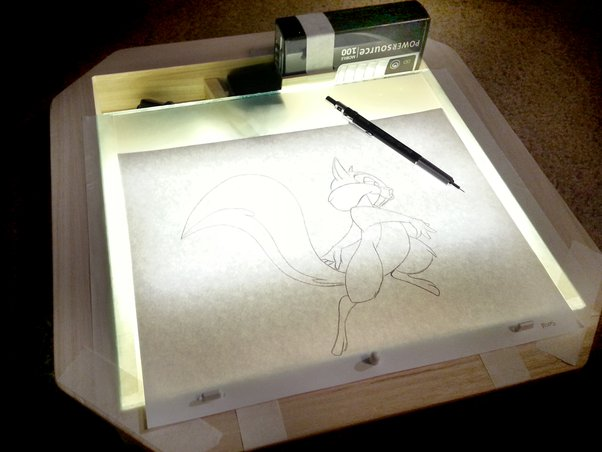
object/refs/main-qimg-91e87c5d25ec91576e7c80ea1fdd794d-pjlq.jpg
