pensthiel/head-md-future-of-drawing/object/refs/Milt Kahl Flipping Thumper.gif

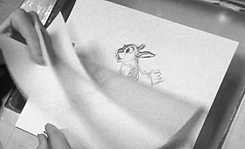
object/refs/Milt Kahl Flipping Thumper.gif
