pensthiel/head-md-future-of-drawing/object/refs/Plexiglass_disc2.jpg

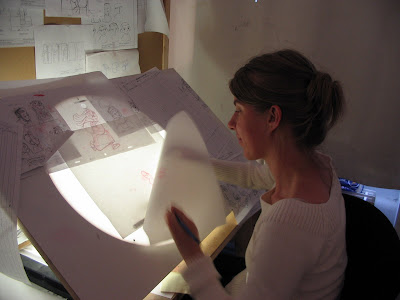
object/refs/Plexiglass_disc2.jpg
