pensthiel/head-md-future-of-drawing/object/refs/Salesforce10.jpg

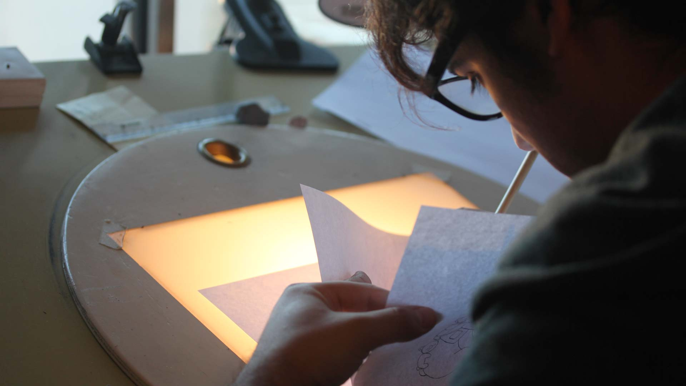
object/refs/Salesforce10.jpg
