pensthiel/head-md-future-of-drawing/object/sketches/Screenshot 2023-12-05 at 11.47.39.png

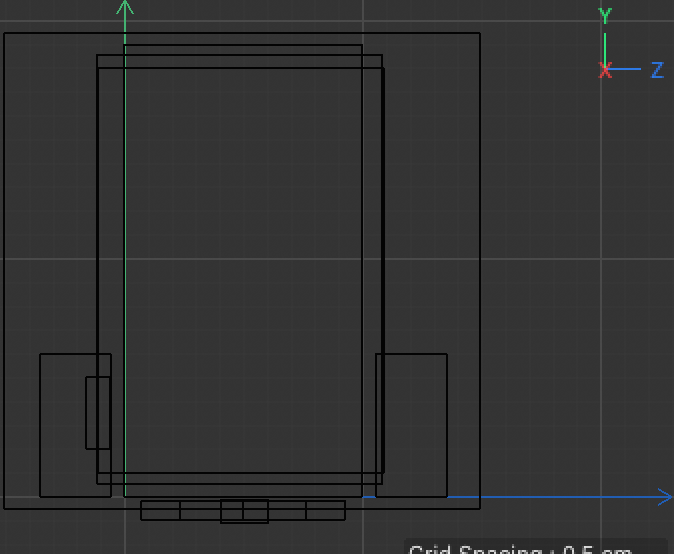
object/sketches/Screenshot 2023-12-05 at 11.47.39.png
