pensthiel/head-md-future-of-drawing/object/sketches/Screenshot 2023-12-05 at 11.48.04.png

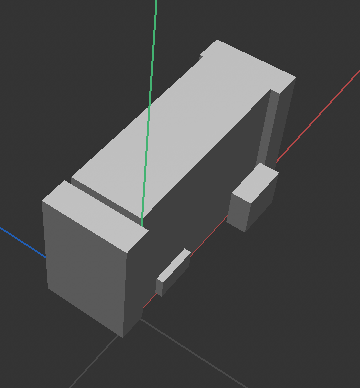
object/sketches/Screenshot 2023-12-05 at 11.48.04.png
