pensthiel/head-md-future-of-drawing/process/2023-10-16-first-ideas/IMG_0852.jpg

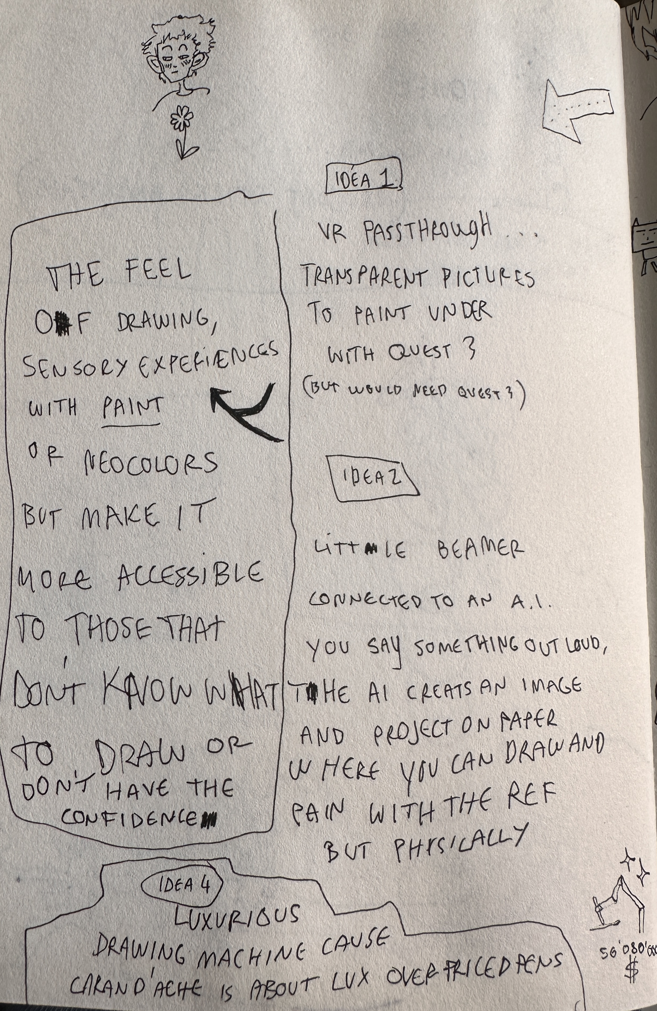
process/2023-10-16-first-ideas/IMG_0852.jpg
