pensthiel/head-md-future-of-drawing/process/2023-10-18-visite-carendache/IMG_0769.JPG

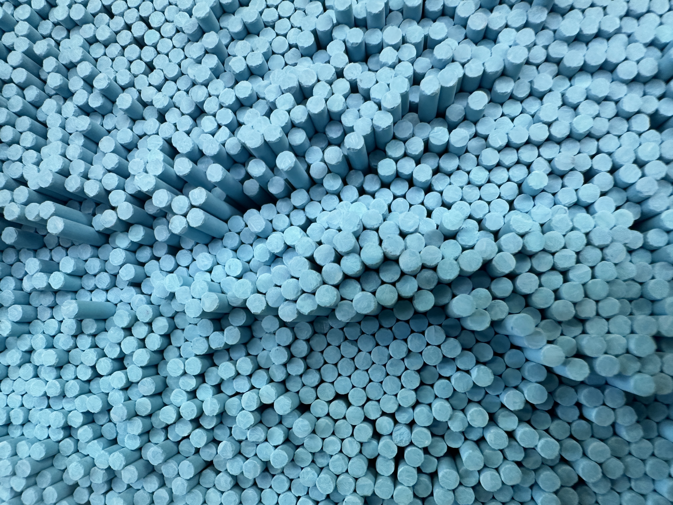
process/2023-10-18-visite-carendache/IMG_0769.JPG
