pensthiel/head-md-future-of-drawing/process/2023-10-18-visite-carendache/Screenshot 2023-10-31 at 11.38.34.png

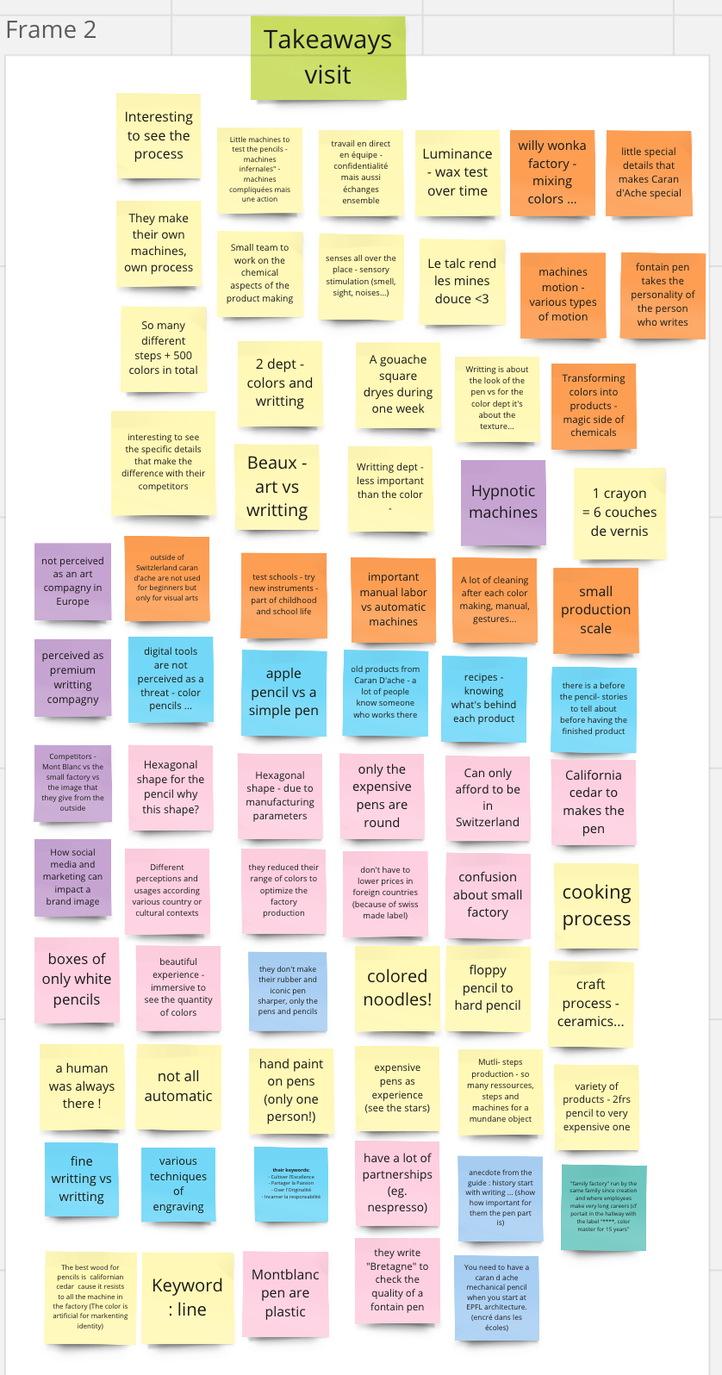
process/2023-10-18-visite-carendache/Screenshot 2023-10-31 at 11.38.34.png
