pensthiel/head-md-future-of-drawing/process/2023-10-18-visite-carendache/Screenshot 2023-10-31 at 11.39.02.png

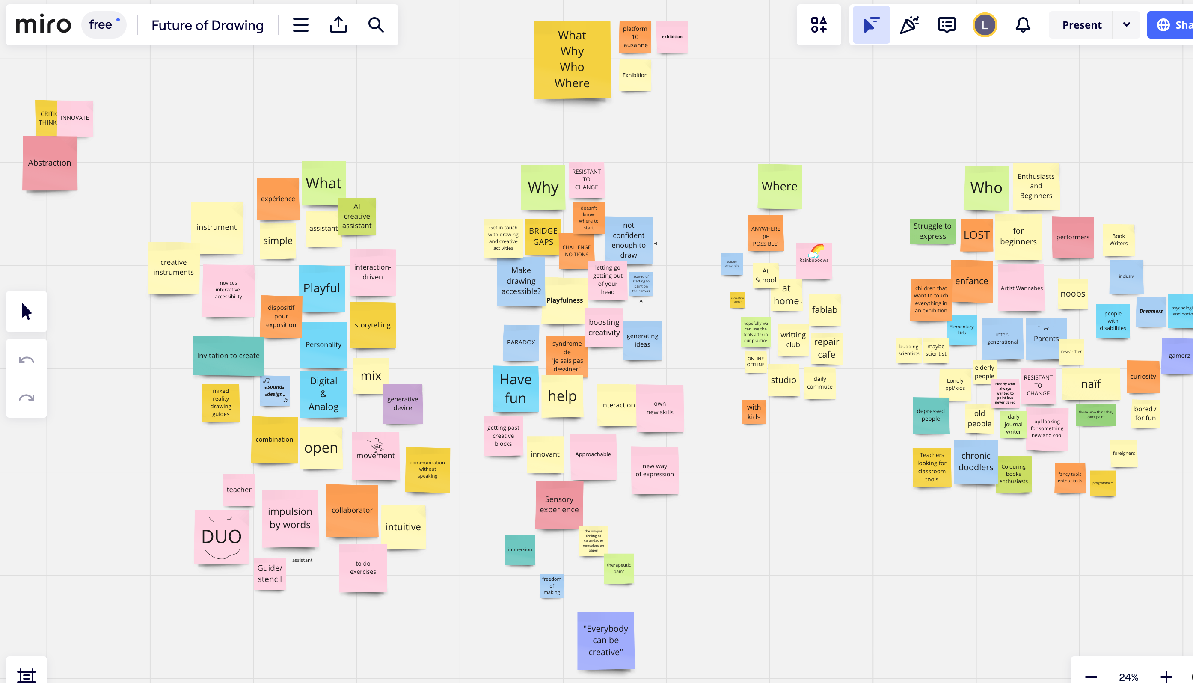
process/2023-10-18-visite-carendache/Screenshot 2023-10-31 at 11.39.02.png
