pensthiel/head-md-future-of-drawing/process/2023-10-20-field-research/Field research - 4.jpg

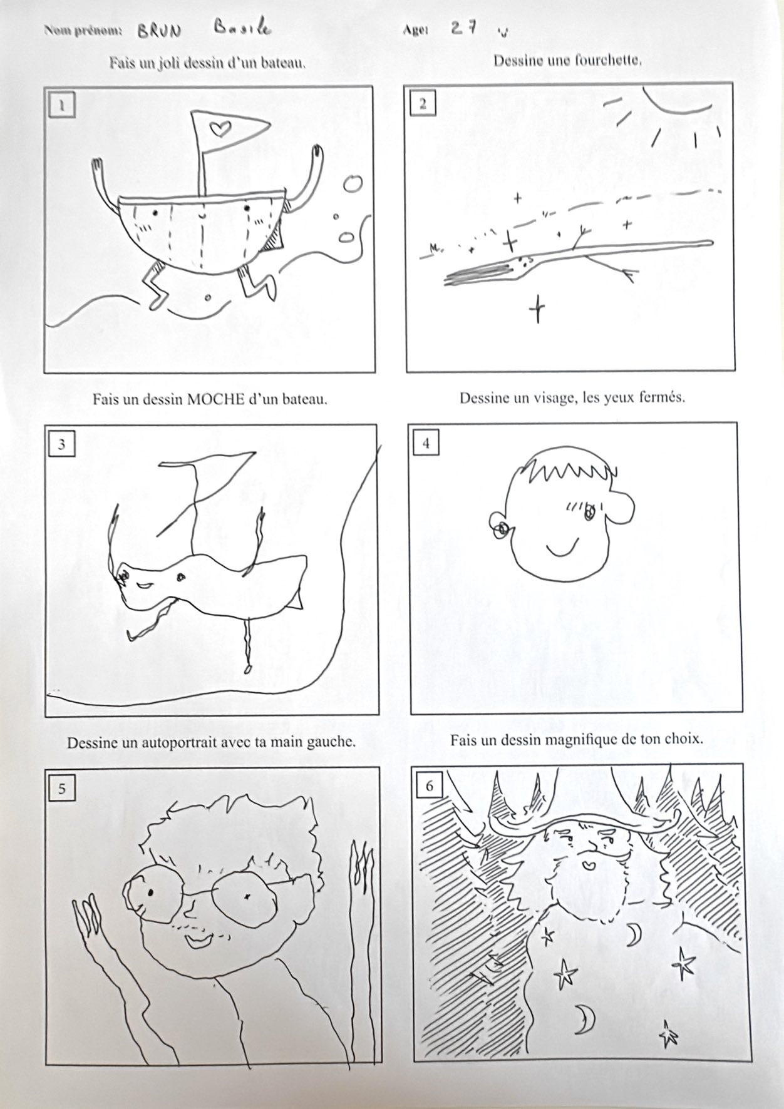
process/2023-10-20-field-research/Field research - 4.jpg
