pensthiel/head-md-future-of-drawing/process/2023-10-20-field-research/Screenshot 2023-10-31 at 11.36.23.png

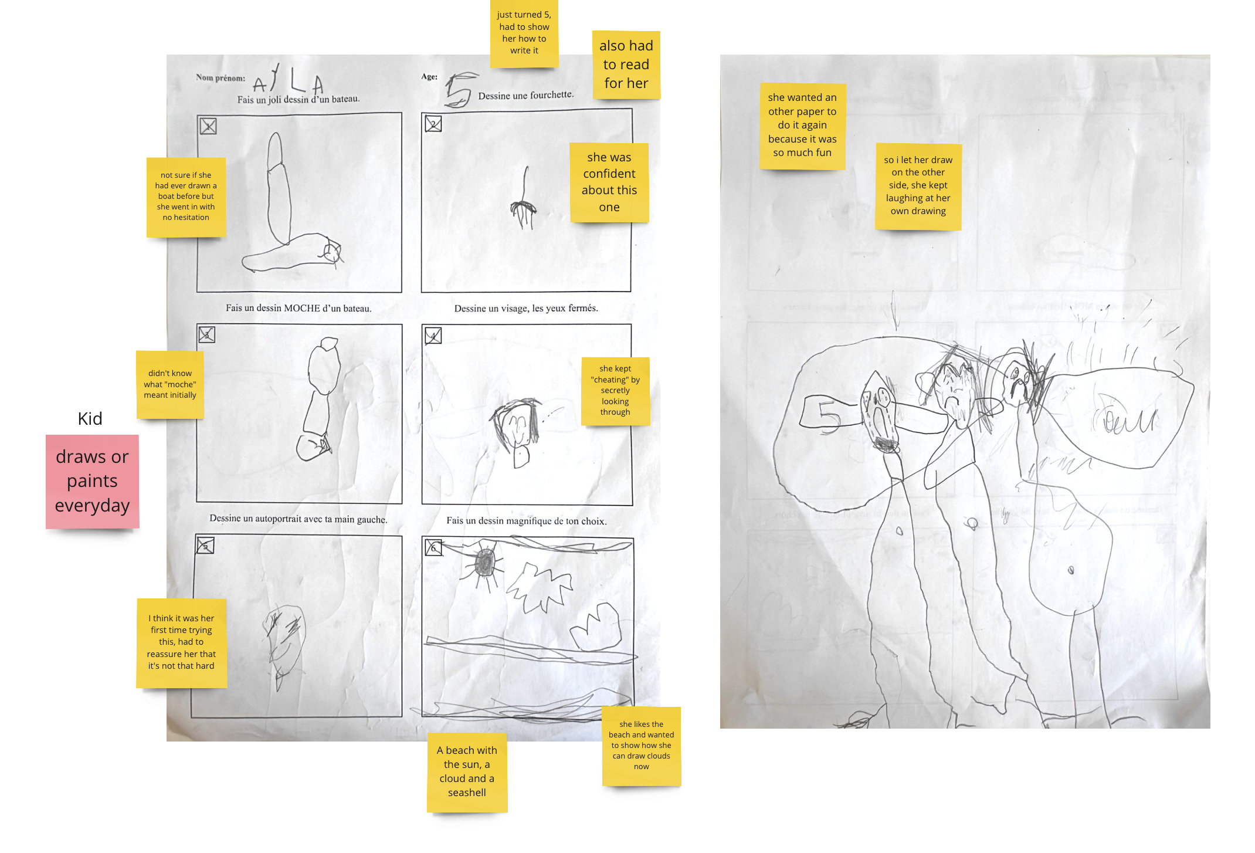
process/2023-10-20-field-research/Screenshot 2023-10-31 at 11.36.23.png
