pensthiel/head-md-future-of-drawing/process/2023-10-26-cards+prototype/IMG_0849.jpg

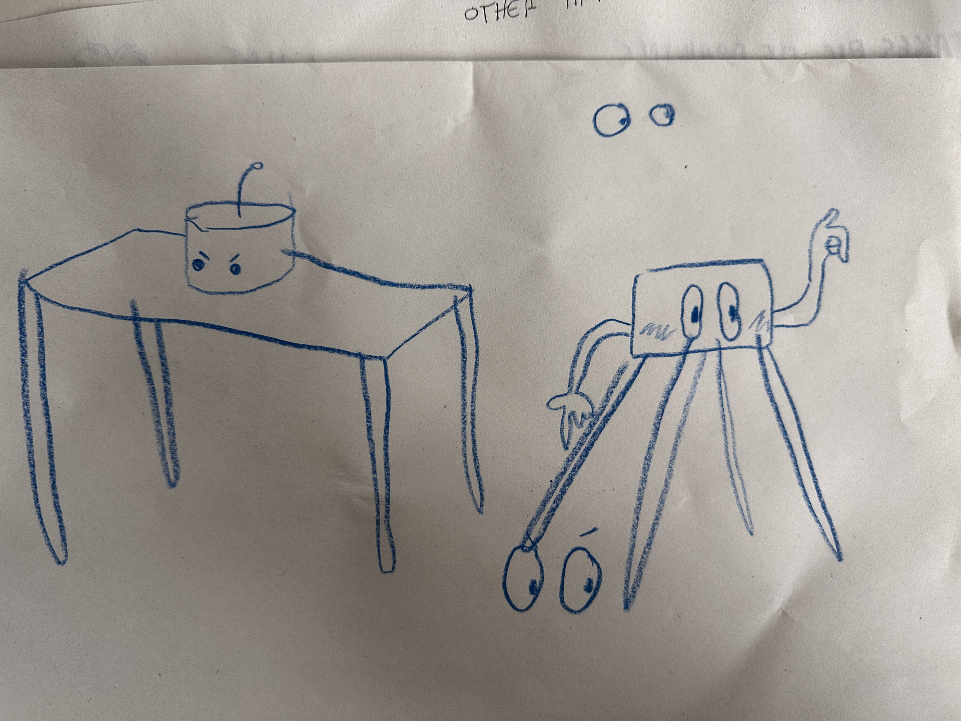
process/2023-10-26-cards+prototype/IMG_0849.jpg
