pensthiel/head-md-future-of-drawing/process/2023-10-30-ideas+text/image.jpg

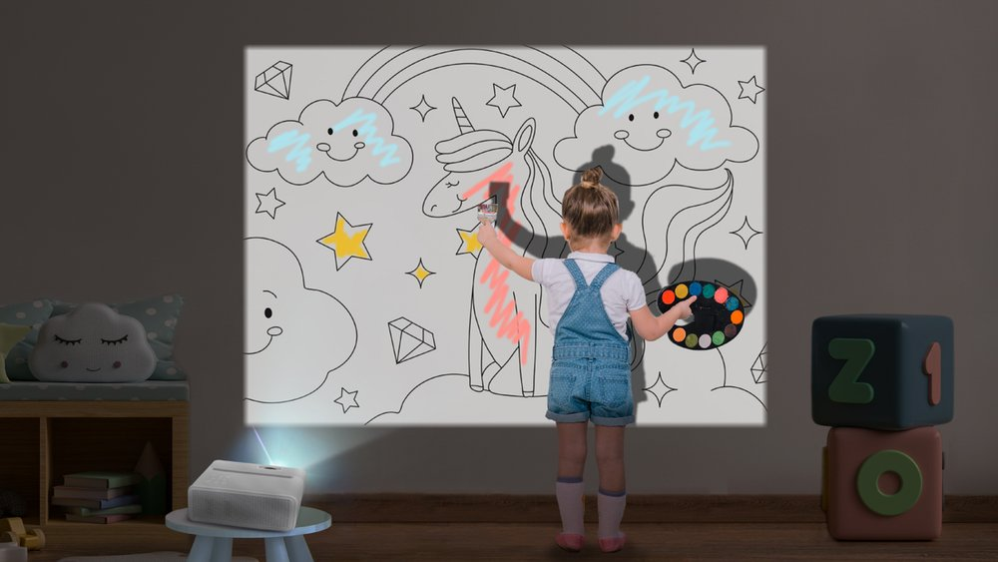
process/2023-10-30-ideas+text/image.jpg
