pensthiel/head-md-future-of-drawing/process/2023-10-30-ideas+text/IMG_0850.jpg

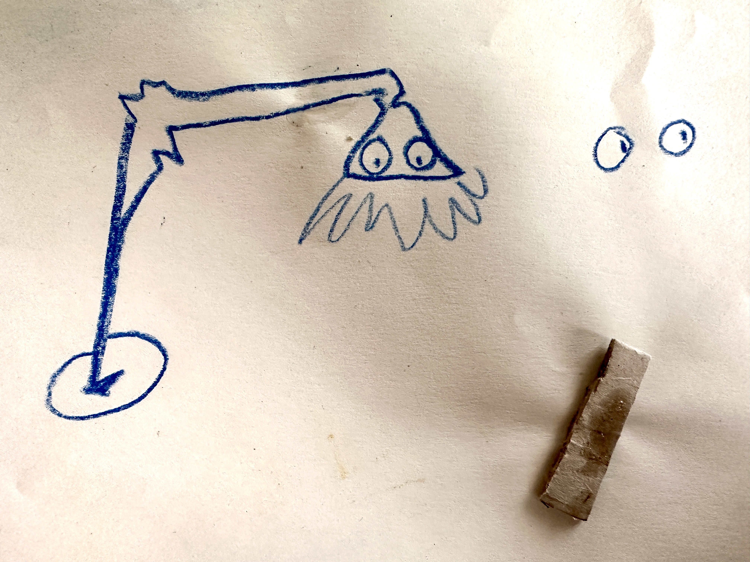
process/2023-10-30-ideas+text/IMG_0850.jpg
