pensthiel/head-md-future-of-drawing/process/2023-11-13/IMG_1004.jpg

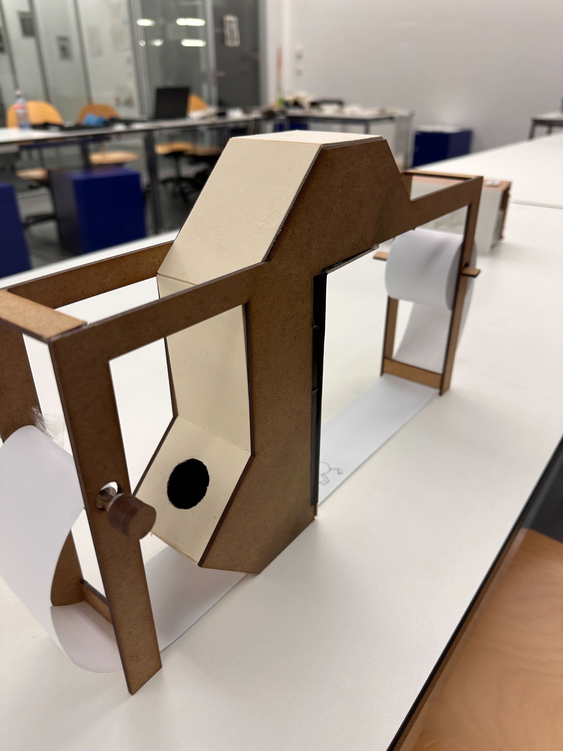
process/2023-11-13/IMG_1004.jpg
