pensthiel/head-md-future-of-drawing/process/2023-11-13/IMG_1011.jpg

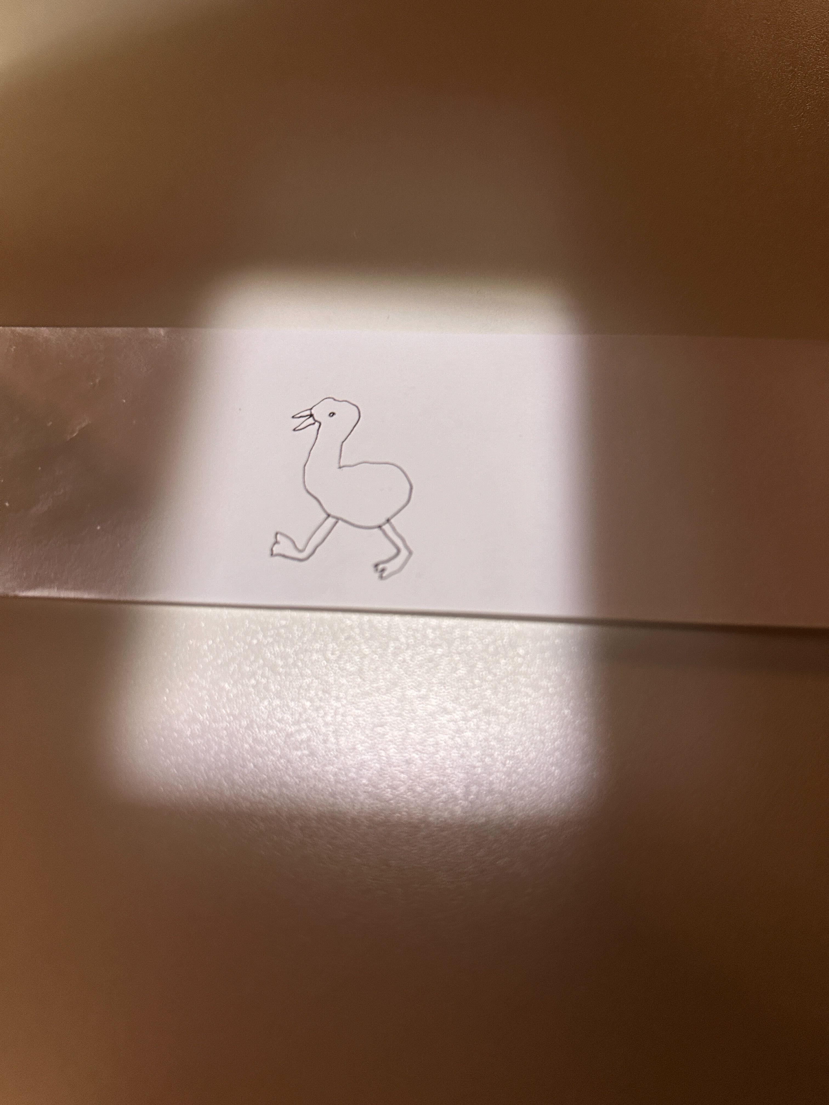
process/2023-11-13/IMG_1011.jpg
