pensthiel/head-md-future-of-drawing/process/2023-11-14/flipbook/anim2.gif

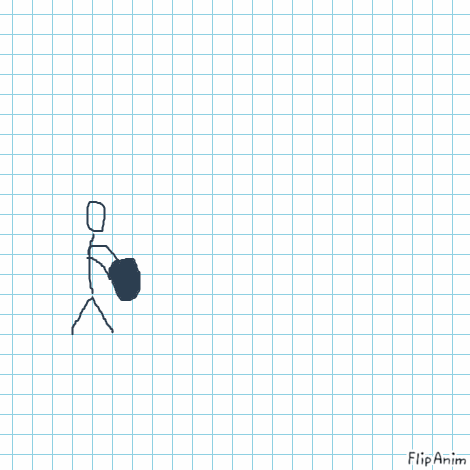
process/2023-11-14/flipbook/anim2.gif
