pensthiel/head-md-future-of-drawing/process/2023-11-14/IMG_0990.jpg

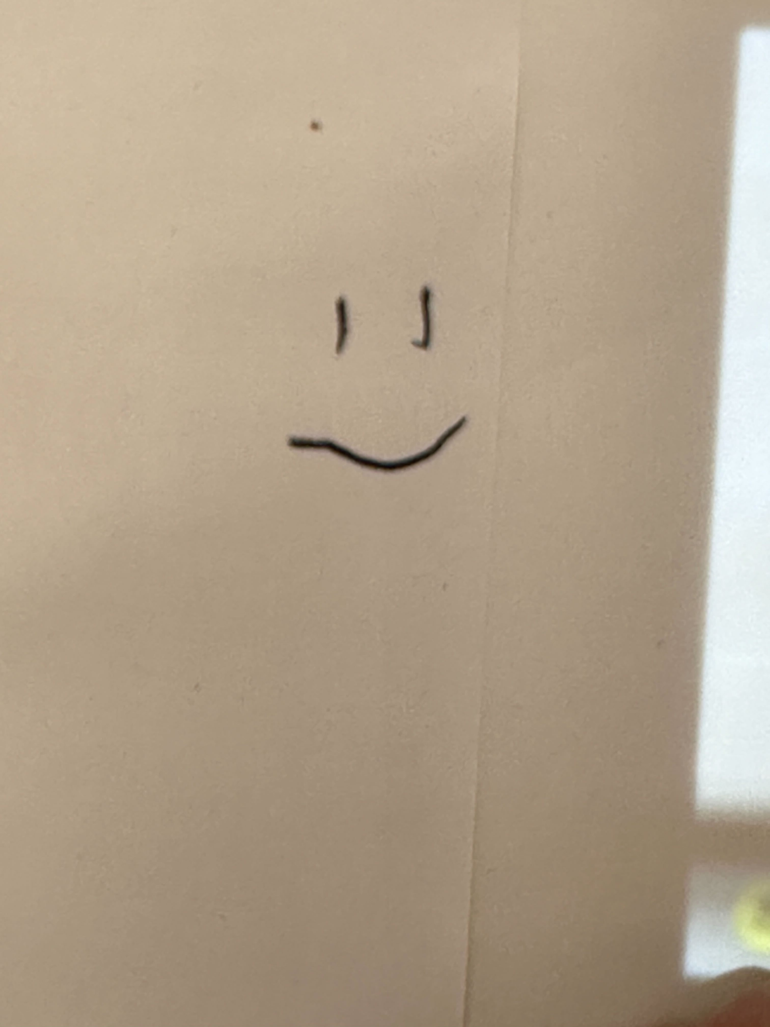
process/2023-11-14/IMG_0990.jpg
