pensthiel/head-md-future-of-drawing/process/2023-11-14/IMG_0991.jpg

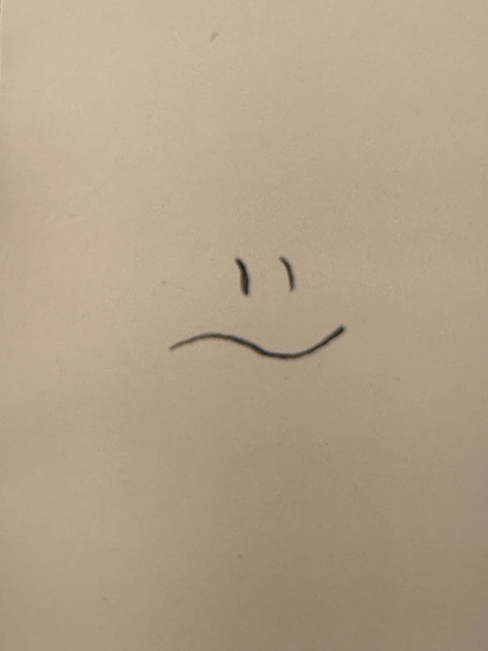
process/2023-11-14/IMG_0991.jpg
