pensthiel/head-md-future-of-drawing/process/2023-11-15/IMG_1022.jpg

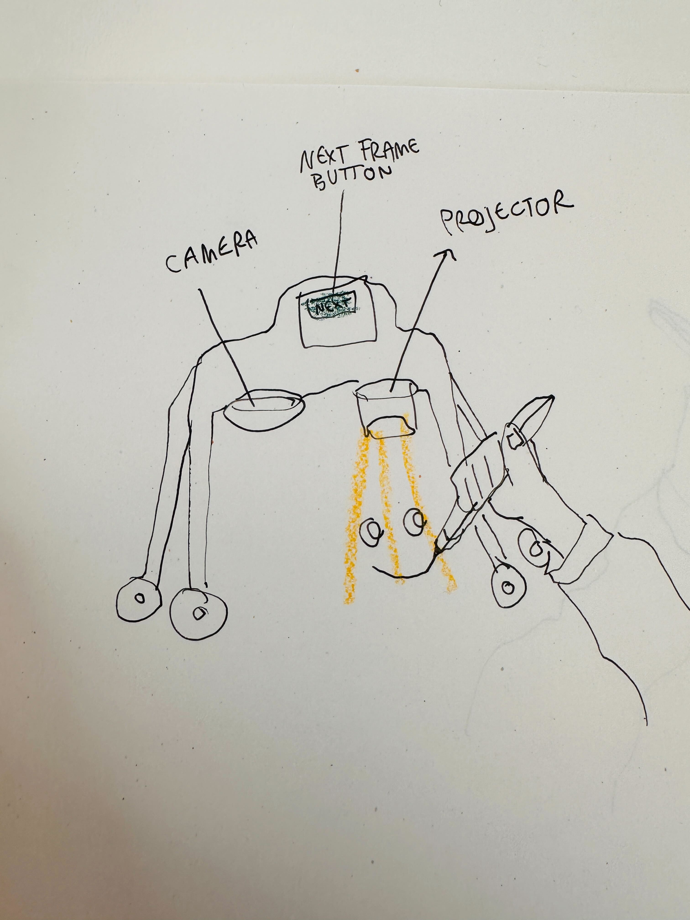
process/2023-11-15/IMG_1022.jpg
