pensthiel/head-md-future-of-drawing/process/2023-11-15/IMG_1024.jpg

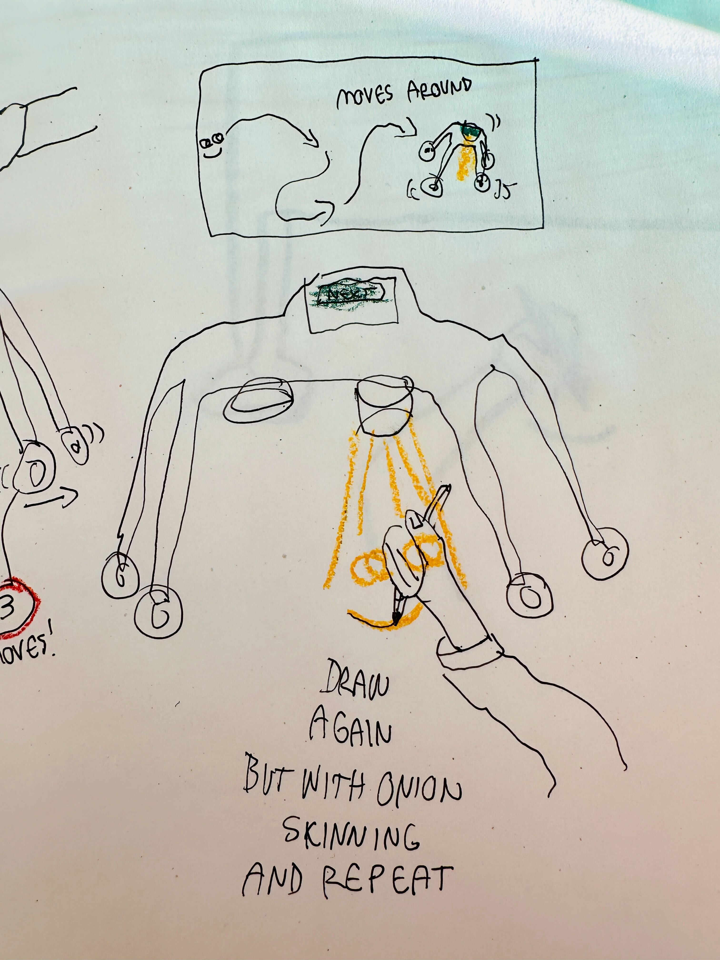
process/2023-11-15/IMG_1024.jpg
