pensthiel/head-md-future-of-drawing/process/2023-12-06/IMG_1221.JPG

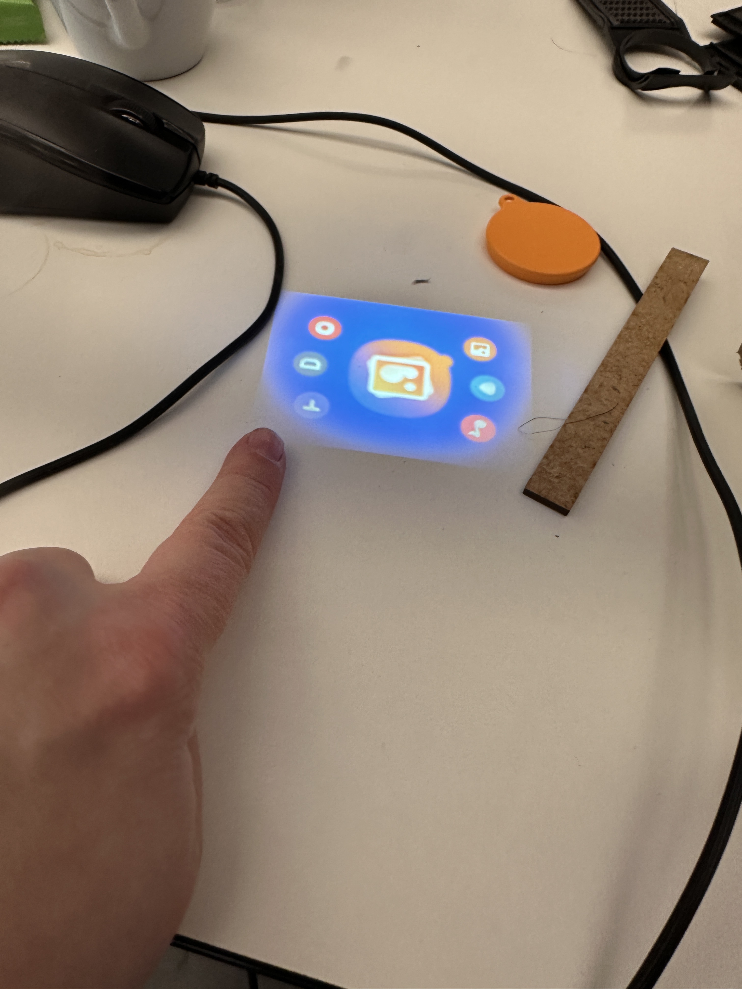
process/2023-12-06/IMG_1221.JPG
