pensthiel/head-md-future-of-drawing/object/360-tests/91.png

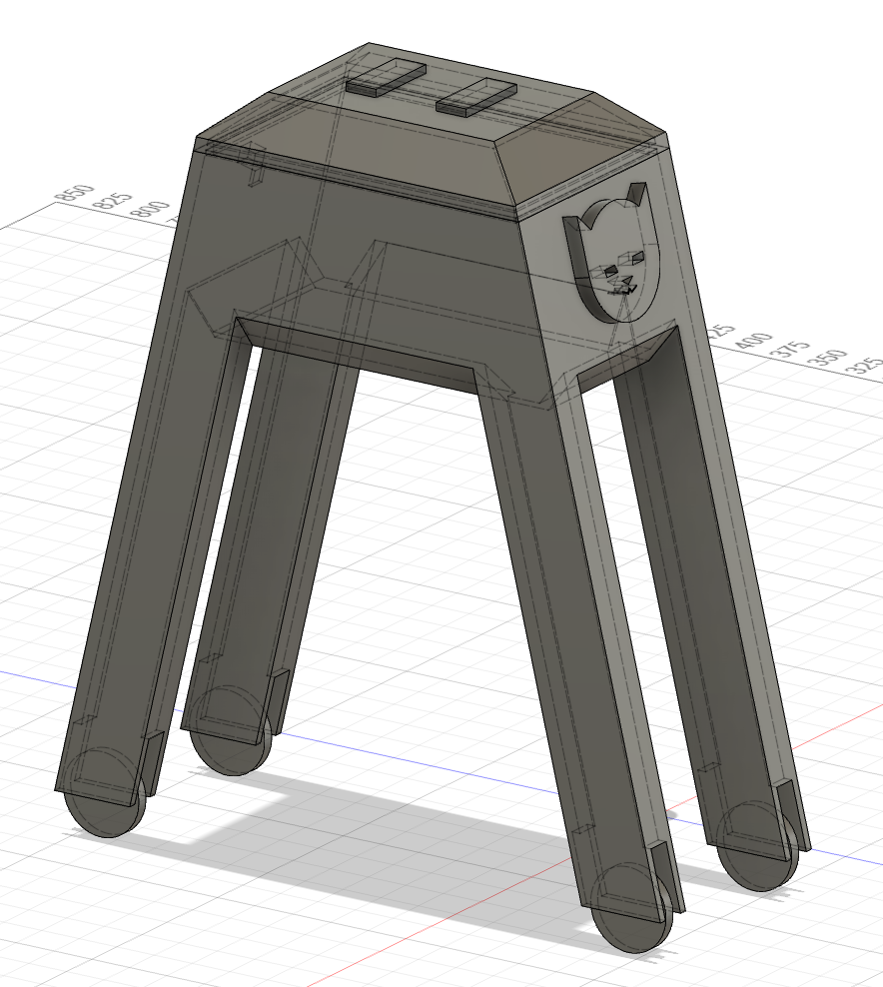
object/360-tests/91.png
