pensthiel/head-md-future-of-drawing/namur/IMG_6986.jpg

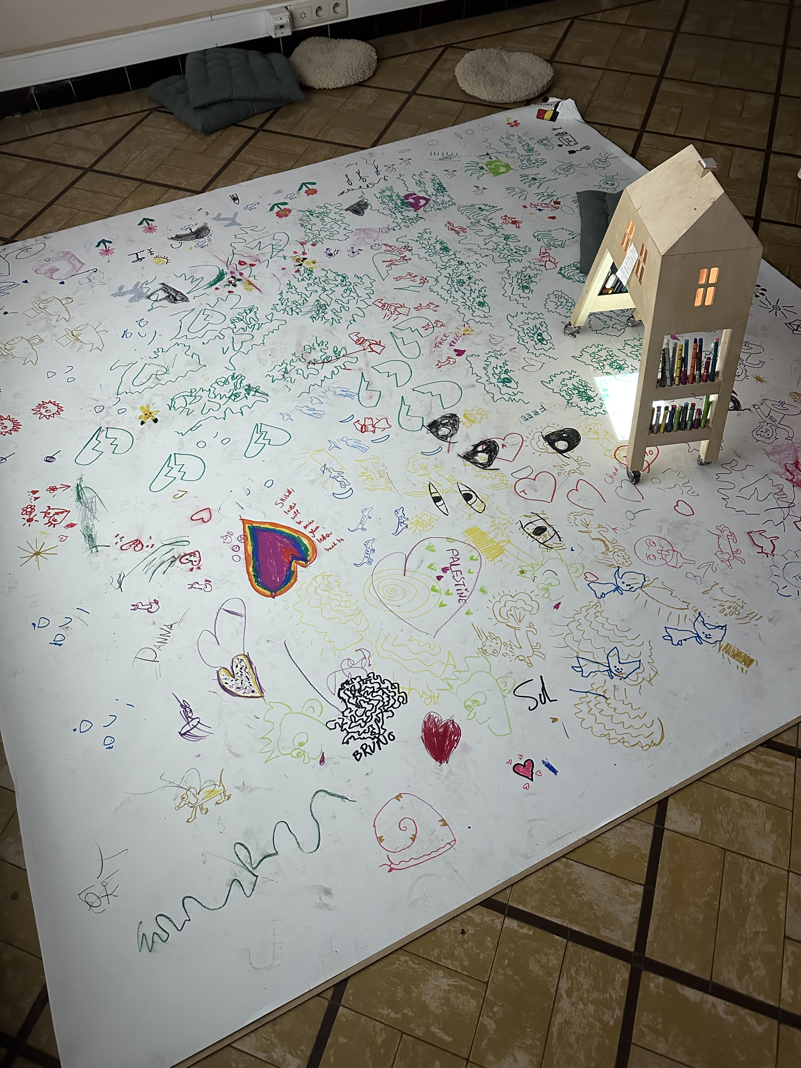
namur/IMG_6986.jpg
