pensthiel/head-md-future-of-drawing/object/photos/IMG_1562.JPG

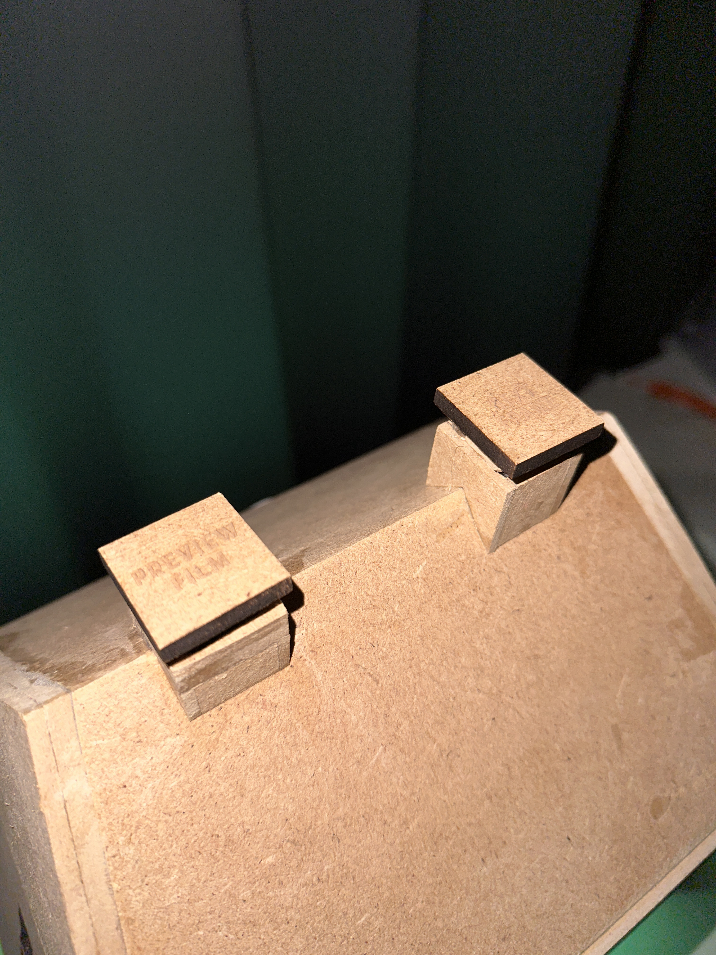
object/photos/IMG_1562.JPG
