pensthiel/head-md-future-of-drawing/object/photos/IMG_1566.JPG

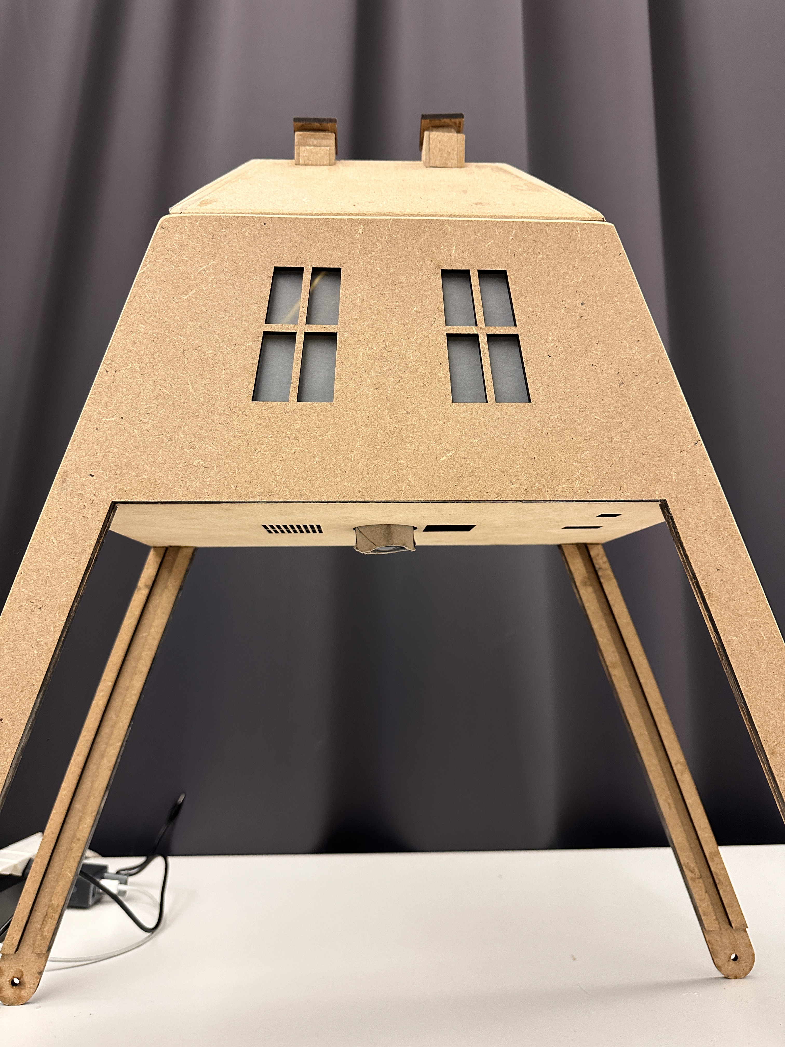
object/photos/IMG_1566.JPG
