pensthiel/head-md-future-of-drawing/object/photos/IMG_1567.JPG

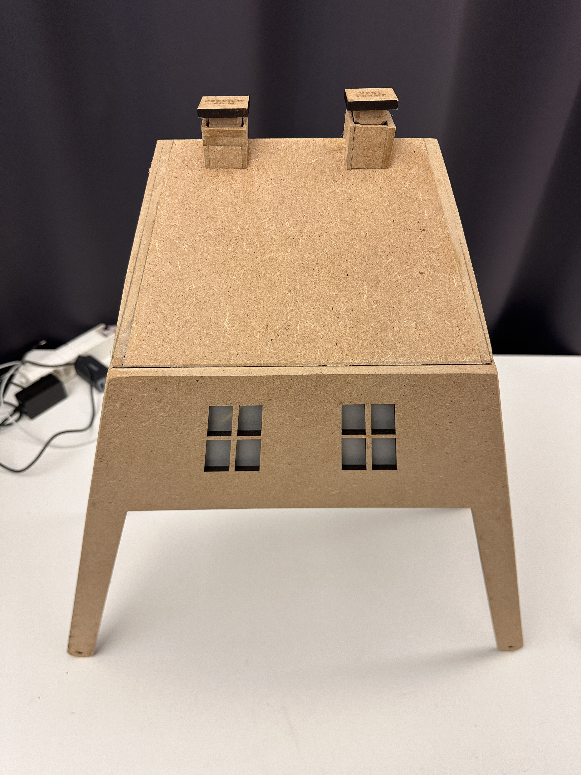
object/photos/IMG_1567.JPG
